tibm/clock/power_values.md

# Power & Passive Values (schematic-ready)

Component values derived from the datasheets in [`/datasheet`](datasheet/) for **this design's** rails.
Everything here is computed for our operating points (VBUS 15 V, 1S Li-ion, the rail set in
[`power.md`](power.md)). ⚠️ = verify/validate on bench or against the noted datasheet section.

---

## 1. LT3652 — 1S buck charger (VIN = VBUS 15 V, float 4.05 V, I_CHG 1.0 A)
Datasheet `charger_lt3652.pdf`. V_FB reference = **3.3 V**. Float set by a divider BAT→V_FB→GND.

| Item | Value | Basis |
|---|---|---|
| **R_FB1** (BAT→V_FB, top) | **45.3 k** (1 %) | V_BAT = 3.3·(1+R_FB1/R_FB2); ratio 0.2265 → 4.047 V |
| **R_FB2** (V_FB→GND, bottom) | **200 k** (1 %) | divider drain ≈ 16.5 µA (always-on, even on battery) |
| **C_FF** feedforward | **22 pF** C0G, BAT→V_FB | datasheet: 20–50 pF to reject V_FB stray-C noise |
| **Full-charge FET** (Decision #2) | **976 k** (1 %) in ∥ with R_FB2, switched by a **2N7002** NMOS | ON → 4.20 V "full"; OFF → 4.05 V health cap. Gate = `FULLCHG_EN` (expander) |
| **R_SENSE** (SENSE–BAT) | **0.1 Ω**, ≥0.25 W (2010/2512) | R_SENSE = 0.1 V / I_CHG(max) → I_CHG = 1.0 A (~0.3 C, cool, safe for any cell) |
| **C_TIMER** (TIMER→GND) | **0.1 µF** | ≈3 h EOC; precondition timeout = t_EOC/8 ⚠️ verify vs. TIMER eq. |
| **Inductor** (SW) | **10 µH**, I_sat ≥ 2 A, low DCR | L=(10·R_SENSE/ΔI)·V_FLT·[1−V_FLT/V_IN], ΔI=0.3 → 9.9 µH |
| **Rectifier** (SW→GND) | **Schottky ≥1 A / ≥30 V** (B340A, 40 V/3 A) | I_D > I_CHG·(V_IN−V_PRE)/V_IN = 0.81 A; V_R > V_IN |
| **C_BOOST** (BOOST→SW) | **1 µF** X7R | + refresh Schottky BAT→BOOST (BAT46); no zener (float < 8.4 V) |
| **C_VIN** | **2×10 µF / 25 V** X7R low-ESR | RMS ripple = I_CHG/2 = 0.5 A worst case; TVS SMAJ22CA already on VBUS |
| **C_BAT** | **10 µF/10 V X7R + 100 µF/10 V polymer** | 100 µF bulk **required** because we run system load with no cell |
| **VIN_REG UVLO** | R_IN1 = **316 k**, R_IN2 = **100 k** | V_IN(min) = 2.7·(R_IN1/R_IN2 + 1) ≈ 11.2 V → charger backs off if the 15 V contract sags. *(Alt: tie VIN_REG→VIN to disable.)* |
| **NTC** | NCP18XH103 (10 k, B25/50 = 3380) NTC→GND **+ 909 Ω (0.91 k, 1 %) in series** | LT3652 NTC pin **sources 50 µA**; trips at **1.36 V (0 °C, cold)** / **0.29 V (40 °C, hot)**. Bare 10 k → 0/40 °C; **datasheet: adding 0.91 k series raises the hot cutoff to 45 °C** → **0/45 °C window** ✓ (cold end ≈ 0 °C, series R negligible there) |

> ⚠️ **Constraint:** the LT3652 needs **V_IN ≥ V_BAT + 3.3 ≈ 7.35 V** to charge. So charging (and
> **no-cell operation**) works **only on the 15 V PD contract**. On the 5 V fallback the charger
> idles — the system then requires a cell. Document on silkscreen/firmware.

---

## 2. CH224K — USB-PD sink (request 15 V)
Datasheet `pd_sink_ch224k.pdf` §5.2.1 / §6.1. Single-resistor mode.

| Item | Value | Basis |
|---|---|---|
| **CFG1** (→GND) | **56 kΩ** | table: 6.8 k=9 V · 24 k=12 V · **56 k=15 V** · NC=20 V |
| **CFG2, CFG3** | **NC** (floating) | single-resistor mode |
| **VDD** | **1 kΩ** from VBUS + **1 µF** VDD→GND | datasheet ref schematic |
| **VBUS sense pin** | **10 kΩ** series to VBUS rail | — |
| **PG** (open-drain) | **10 kΩ** pull-up to 3V3 → `PD_PG` (expander) | active-low power-good |
| **CC1 / CC2** | to Type-C CC1 / CC2 | CH224K provides the PD/CC |
| **DP / DM** | **short together at CH224K**; route Type-C D± to **ESP32 IO19/20** | §5.5 PD-only mode → native USB free for the MCU |

---

## 3. TPS61023 — 5 V boost (from BAT, always-on)
Datasheet `boost_5v_tps61023.pdf`. V_REF (FB) ≈ **0.6 V**. Load ≈ 0.5–1.0 A worst case (feeds 3V3 buck + stepper VM + 7× SK6812 ≤0.6 A all-white + EM14 encoder ~30 mA) — well inside the 3.7 A valley limit.

| Item | Value |
|---|---|
| **R1** (VOUT→FB) | **732 k** (1 %) — datasheet 5 V value |
| **R2** (FB→GND) | **100 k** (1 %) → V_OUT = 4.99 V |
| **C_FF** (∥R1) | **220 pF** *optional* (only if loop rings; f_z ≈ 1 kHz) |
| **L1** | **1 µH**, I_sat ≥ 2 A, low DCR (Coilcraft XEL4030-102ME / Würth 74438357010) |
| **C_IN** | **10 µF / 10 V** X7R |
| **C_OUT** | **2 × 22 µF / 10 V** X7R |
| **EN** | tie to **BAT** (rail is always-on) |

---

## 4. TLV62569 — 3.3 V buck (from 5 V)
Datasheet `buck_3v3_tlv62569.pdf`. V_FB = **0.6 V**. V_OUT = 0.6·(1+R1/R2).

| Item | Value |
|---|---|
| **R1** (VOUT→FB) | **453 k** (1 %) |
| **R2** (FB→GND) | **100 k** (1 %) → V_OUT = 3.32 V |
| **C_FF** C3 (∥R1) | **6.8 pF** (datasheet rec for R2 = 100 k) |
| **L** | **2.2 µH**, I_sat ≥ 2.6 A (Table-4 "++" combo) |
| **C_IN** | **10 µF / 10 V** X7R |
| **C_OUT** | **22 µF / 10 V** X7R |

---

## 5. TPS55340 — 12 V boost (from BAT, **plugged-only**, audio PVDD + wake LEDs)
Datasheet `boost_12v_audio_tps55340.pdf`. V_REF = **1.229 V**. Datasheet worked a 12 V/1 A example — reuse it.

| Item | Value | Basis |
|---|---|---|
| **R1** (VOUT→FB) | **86.6 k** (1 %) | V_OUT = 1.229·(1+R1/R2) = 11.87 V |
| **R2** (FB→GND) | **10 k** (1 %) | — |
| **R4** (FREQ/RT) | **95.3 k** → **500 kHz** | datasheet Eq 1 |
| **C_SS** (soft-start) | **0.047 µF** | datasheet |
| **Comp: R3 / C4 / C5** | **2.55 k / 0.1 µF / 100 pF** ⚠️ | 6 kHz BW example; validate on bench |
| **Inductor** | **4.7 µH**, I_sat ≥ **6 A**, low DCR ⚠️ | boost from 1S: I_IN ≈ 4–4.7 A |
| **Diode** (SW→OUT) | **Schottky ≥3 A / ≥30 V** (B340A/B340B, 40 V/3 A) | peak ~5 A |
| **C_OUT** | **3 × 22 µF / 25 V** X7R (1210) | 60 mV ripple, 30 µF eff. after derating |
| **C_IN** | **10 µF/10 V X7R + 0.1 µF + 100 µF/10 V bulk** | high input current |
| **EN** | `BOOST12_EN` (expander) + **100 k pulldown** (off at boot) | true shutdown; **plugged-only** — firmware asserts only when `PD_PG` is live (off on battery) |

> ⚠️ **Constraint:** boosting a single cell (3.0–4.2 V) to 12 V at ~1 A draws **~4–4.7 A input**,
> near the TPS55340's 5.25 A FET limit at low battery → max ~0.9–1 A (≈10–12 W). Even plugged, the
> input is the BAT node (~4.05 V), so the **~12 W ceiling holds** and is now **shared by wake LEDs +
> audio** → firmware keeps their sum ≤ ~12 W (the amp's power foldback covers any shortfall). On
> battery the boost is **off** (plugged-only); the amp drops to the 5 V rail (§8 mux). Don't spec >12 W.

---

## 6. Small analog / support networks

| Block | Values |
|---|---|
| **32.768 kHz XTAL** (ABS07, C_L 12.5 pF) | 2 × **18 pF** C0G load caps (= 2·(C_L − C_stray), C_stray ≈ 3 pF); no series R; ESR ≤ 70 kΩ |
| **Vbat ADC divider** (+ disconnect FET, Decision #3) | R_top **100 k**, R_bot **100 k** (÷2: 4.2 V→2.1 V, ADC1 11 dB atten) + **100 nF** at node. **2N7002** in series with R_bot→GND, gate = `VBAT_DIV_EN` (expander) → off in deep-sleep (saves ~21 µA). **D13 BAT42W (SOD-123)** clamp, cathode on the node → bounds a reversed-cell excursion to ~−0.2 V (added 2026-07-21) |
| **CELL_TEST** (full-cell vs no-cell, added 2026-07-21) | Expander GPB7 → **Q8 2N7002** (gate PD **R26 100 k**) pulls **Q9 AO3401A**'s gate low (G-S pull-up **R27 100 k**); Q9 source = holder+, drain = Q2's gate → asserting lifts Q2's gate to holder+ → **Q2 off**. ADC step at switch-off ≥ ~0.3 V ⇒ empty holder (body-diode back-feed); ≤ ~50 mV ⇒ real cell. Plugged-only, brief; POR-safe (both FETs default off) |
| **USB D± ESD** (added 2026-07-21) | **USBLC6-2SC6** flow-through at J1: D− → pin 1 / out pin 6 → IO19, D+ → pin 3 / out pin 4 → IO20, GND pin 2. **VBUS pin 5 = NC on purpose** — our VBUS is the 15 V contract vs the pin's 5.25 V rating; the internal zener still clamps, and a cable VBUS-to-D± fault burns the (sacrificial) array instead of pumping a rail |
| **QRE1113GR homing** | IR-LED ballast **150 Ω** (V_F 1.2 V → I_F ≈ 14 mA @ 3V3); phototransistor collector→3V3 via **10 k**, output→ADC (IO2) + **100 nF**. Tune 10 k for distance/reflectivity |
| **Reverse P-FET** (AO3401A) | source=holder+, drain=system BAT+; gate→GND **100 k**; optional 8–10 V Zener gate-source clamp |
| **Protector** (HY2111 + AOSD32334C) | **R1** (batt+→VDD, supply stabilize/ESD) **100 Ω** + **C1** (VDD–VSS) **0.1 µF** (datasheet §10: R1 100–200 Ω — too large degrades detect accuracy and risks VDD abs-max on a reversed charger; C1 ≥ 0.01 µF); **R2** (CS→P−, charger/current sense) **2 kΩ** (§10: 1–2 kΩ — larger can prevent cutting charge current with a high-voltage charger); AOSD32334C dual-N in cell− path, gates from **OD** (discharge FET) / **OC** (charge FET). **No external delay caps** — HY2111 delays are internal. Thresholds fixed by suffix **-GB = OV 4.28 V (rel 4.08) / OD 2.90 V / OC 150 mV**. SOT-23-6 pinout: OD1·CS2·OC3·NC4·VDD5·VSS6 *(same arrangement as the replaced AP9101C — nets unchanged)* |
| **Knob (EM14A0D-C24-L064S, 5 V)** | A/B outputs are 5 V logic → **divider 100 k series + 200 k → GND** per channel (node ≈ 3.2 V → IO47/48 PCNT; ~67 k source Z is fine at ≤ a few hundred Hz quadrature); **ENC_SW** dry contact → **10 k PU to 3V3 + 100 nF** at IO17 (+ ~5 ms FW debounce) |
| **I²C pull-ups** | main board **4.7 kΩ ×2** (SDA/SCL) @ 3V3. Sensor breakouts add 10 k each in ∥ — lift their jumpers if the bus gets too strong |
| **ESP32 EN** | **10 kΩ** PU + **1 µF** to GND (+ optional reset button) |
| **ESP32 straps** | IO0: **10 kΩ** PU (+ boot button); IO45/IO46 (the wake PWM lines) sit low at boot via their AO3400A gate nets (R105/R107 = 100 Ω + 10 k ≈ **10.1 kΩ to GND** at the pin) + the S3 internal strap PD — **no dedicated pulldown** (R52 dropped 2026-07-25 as redundant); IO3 internal |

---

## 7. Decoupling plan (per IC)

| IC / rail | Decoupling |
|---|---|
| ESP32-S3 3V3 | **10 µF + 22 µF + 0.1 µF** (module bulk) + 0.1 µF per 3V3 pad |
| TAS5760M | PVDD **0.1 µF + 1 µF + 100 µF/25 V** bulk (C172; **was 220 µF** — no ≥16 V 220 µF exists in the board's Ø6.3 mm SMD can, Panasonic/Nichicon start at Ø8, so the value dropped 2026-07-27 to a **Rubycon 25TZV100M6.3X8** low-ESR part, 300 mA @100 kHz. ⚠ bench: watch PVDD sag on alarm transients; the fix if it sags is a Ø8 land + 220 µF/16 V, not a bigger ceramic); DVDD/AVDD **0.1 µF + 10 µF**; bootstrap + output filter per datasheet |
| TB6612FNG ×2 | VM **0.1 µF + 10 µF**; VCC **0.1 µF** |
| MCP23017 | **0.1 µF** |
| SK6812 chain (7×) | **100 nF at every pixel VDD** + **100 µF bulk** at the chain head; SN74AHCT1G125 **100 nF** |
| Each regulator | in/out caps per §1–5 + 0.1 µF at each VIN pin |

---

## 8. LED subsystem (two rails — see [`led.md`](led.md) + [`power.md`](power.md) §LED)
**2 wake PWM channels + 1 NeoPixel data line** (v0.19 — the 5 V discrete panel string + its 3rd
AO3400A were dropped with the display).

| Channel | Emitter (per `led.md`) | Rail | Pin |
|---|---|---|---|
| **Wake warm** | Inspired LED `12V-COB-3000K-12M` (warm 3000K COB) | **12 V** (plugged-only) | **IO45** (LEDC) |
| **Wake cool** | Inspired LED `12V-COB-4000K-12M` (neutral 4000K COB) | **12 V** (plugged-only) | **IO46** (LEDC) |
| **Status + dial NeoPixels** | **7× SK6812 RGBW 5050** (Adafruit 2758): 5 status + 2 dial | **5 V** (always) | **IO7** (RMT data) |

- **Wake (12 V COB):** `MCU PWM → 100 Ω → AO3400A gate`; `10 kΩ` gate→GND; strip− to FET drain, strip+
  to **12 V**. Self-ballasted (integrated series R) → no external ballast. Keep combined wattage so
  **LED + audio ≤ ~12 W** (TPS55340 ceiling from 1S). ~1 kHz, gamma-corrected.
- **NeoPixels (5 V):** IO7 → **SN74AHCT1G125** (VCC = 5 V; TTL V_IH 2 V ← 3.3 V GPIO OK; the SK6812
  V_IH = 0.7·VDD = 3.5 V is why the buffer exists) → **330 Ω** series → DIN(1); DOUT(n)→DIN(n+1);
  **100 nF per pixel + 100 µF bulk**. `led_strip` (RMT, 800 kHz); ≤~0.6 A all-white worst case.

**Panel string (Cree CLM3C ×≤12 + 180 Ω each + 3rd AO3400A) dropped 2026-07-19.** MOSFET **AO3400A** ×2.

### Amp PVDD rail-mux (12 V ↔ 5 V) — enables the battery alarm
The 12 V boost is **plugged-only**, so on battery the TAS5760M PVDD falls back to the **5 V rail**
(~3 W, quieter alarm). **LTC4412 ideal-diode on the 5 V leg + Schottky on the 12 V leg**; 12 V wins when
present. Pinout (TSOT-23-6): **1 VIN · 2 GND · 3 CTL · 4 STAT · 5 GATE · 6 SENSE**.

| LTC4412 pin / part | Connect to | Basis |
|---|---|---|
| **VIN** (1) | **5 V** rail | primary (backup) source; +**0.1 µF** to GND |
| **SENSE** (6) | **PVDD** node | senses load vs VIN (20 mV fwd-reg / 20 mV reverse-turn-off); +**0.1 µF** |
| **GATE** (5) | gate of **Q_5V** | drives the 5 V→PVDD ideal-diode P-FET (gate clamp V_G(ON) = 7 V) |
| **Q_5V** P-FET | **AO3401A** (reuse) — source = 5 V, drain = PVDD | low-loss; ~36 mΩ×0.6 A ≈ 22 mV → PVDD ≈ 4.96 V (> 4.5 V min). Body diode reverse-blocks when PVDD > 5 V. Lower-R_DS alt (e.g. DMP3017SFG) if tighter reg wanted |
| **CTL** (3) | **GND** | fully automatic SENSE-based switchover (no MCU/expander line) |
| **STAT** (4) | **470 k → 3V3** (optional) or NC | open-drain "12 V-present" flag; can land on a spare expander IN |
| **12 V leg** | 12 V-boost OUT → **Schottky (SS34 / B340A, 40 V, ≥1.5 A)** → PVDD | 12 V has margin for the ~0.4 V drop (PVDD ≈ 11.6 V plugged); blocks 5 V↔12 V back-feed |
| **PVDD bulk** | keep the §7 `0.1 + 1 + 100 µF/25 V` at the amp | mux output = PVDD node |

When 12 V is up, PVDD rises to ~11.6 V > VIN(5 V) → LTC4412 turns Q_5V off (its body diode is also
reverse-biased) → amp on 12 V. On battery the Schottky blocks and Q_5V ideal-diodes 5 V→PVDD.
> A plain 2-diode OR is **rejected**: 5 V − V_Schottky ≈ 4.6 V ≈ the TAS5760M PVDD 4.5 V min (no margin) —
> hence the low-loss FET on the **5 V** leg; the Schottky is only tolerable on the **12 V** leg.

## 10. TAS5760M — control-mode straps, PBTL, gain, output filter (schematic-ready)
Datasheet `amp_tas5760m.pdf` (32-pin DAP). **Software (I²C) control**, **PBTL mono** into the 4 Ω DMA58-4.

| Item | Setting | Basis |
|---|---|---|
| **Control mode** | **Software/I²C** → tie **SPK_GAIN0 (11) + SPK_GAIN1 (12) HIGH to DVDD** (one 10 k pull-up serves both). This reallocates **PBTL/SCL (9) = SCL** and **FREQ/SDA (8) = SDA** as the I²C port | §8.4.2 |
| **I²C address** | **0x6C** → **SPK_SLEEP/ADR (13) → GND** (weak PU, latched at power-up; HIGH = 0x6D). Prep a **0 Ω to GND** | §8.4.2.5.1 |
| **PBTL enable** | firmware sets **reg 0x06 bit 7 = 1** (default 0 = BTL); channel-select = 0x06 bit 1. ⚠ **Corrected 2026-09-13** — the external tie is **OUTA+(29)∥OUTA−(26)** as one leg and **OUTB+(20)∥OUTB−(23)** as the other, speaker between them (datasheet Fig. 64/65). This row previously said OUTA+∥OUTB+ / OUTA−∥OUTB−, which is **wrong**: it shorts a high side to a low side and puts a PVDD→PGND path through 2×120 mΩ every switching cycle. **The board was already right** — `kicad/REVIEW.md` fixed #2 caught it in the schematic (`1f3736a`, refined `1cf1629`) and the PCB followed in the 2026-08-04 sync + routing; only this line was left stale | §8.4.2.3 |
| **Analog gain** | firmware **A_GAIN[3:2] in reg 0x06**; start **19.2 dBV** (matches 12 V PVDD). ⚠ **Digital boost = +0 dB, NOT the default** — corrected 2026-09-13: reg 0x02[5:4] powers up at **01 = +6 dB**, and [`FIRMWARE.md`](FIRMWARE.md) §6.2's whole ceiling table is computed from *0 dBFS = 9.12 V rms*, which is 19.2 dBV **with no boost**. Leaving the default makes every watt in that table 6 dB optimistic, and the 8 W inductor cap depends on it. The firmware writes `0x02 = 0x04`. (SW mode: gain is a register, not a pin) | §8.4.2.4 |
| **Output LC (4 Ω)** | **10 µH + 0.68 µF per leg** (datasheet 4 Ω filter; 8 Ω = 22 µH, 6 Ω = 15 µH), f_c ≈ 30–40 kHz. **L5/L6 = XAL4040-103MEC, Isat 3.0 A** and they carry the full speaker current; the OCE trips at 7 A/BTL (**~14 A in PBTL**), so the amp cannot protect them → the **firmware limiter is capped at 8 W into 4 Ω** (peak 2.0 A + 0.38 A ripple ≈ 79 % of Isat), [`FIRMWARE.md`](FIRMWARE.md) §6.2 | §6.13 |
| **SPK_SD (7)** | from **MCP23017 GPA0** (idle-low = shutdown at boot) | §8.4.2.1 |
| **SPK_FAULT (6)** | open-drain → **10 k PU to 3V3**; optional to a spare expander IN (GPB6) for a HW fault line, else poll fault regs over I²C | §8.3.3.1 |
| **SFT_CLIP (2)** | **tie to GVDD_REG** (soft-clipper off → clip at rail; firmware HPF + limiter + digital clipper protect the driver). Divider+cap only if a fixed soft-clip point is wanted | §8.4.1.3 |
| **Reg pins** | ANA_REG(3)/GVDD_REG(32)/VCOM(4)/ANA_REF(5): **bypass caps only — do not load** | §8.3.1 |
| **AVDD (1)** | ⚠ **→ PVDD, NOT +3V3.** Added 2026-09-14 after build #1 made no sound. §6.3 Recommended Operating Conditions gives **AVDD 4.5–26.4 V** — the same range as PVDD; only **DVDD** is 2.8–3.63 V. §10's prose ("two power supplies") reads as if there were no third supply pin, and that is the trap: three supply PINS, two RAILS. Figure 64 routes pin 1 to the PVDD node. **The board ties it to +3V3 — 1.2 V under minimum** — which leaves the digital domain alive (I²C fine) and the analog domain dead (reg 0x08 stuck at CLKE). `kicad/REVIEW.md` **V13** carries the fix and the bench bodge | §6.3 / Fig. 64 |
| **MCLK (14)** | TAS5760M **requires MCLK (128–512 × f_S)** — not MCLK-less. **`IO43` = `I2S_MCLK`** (HW I²S0 via the S3 GPIO matrix; reassigned from the aux UART log → logging = USB-CDC only). Target **256 f_S ≈ 12.288 MHz @ 48 kHz** | §8.3.2.1 / Table 6 |

---

## 9. Speaker output filter (Decision #4 → **LC, recommended**)

| Option | Per BTL output | ~Cost | Trade |
|---|---|---|---|
| **Full LC** ✅ | **L 10–22 µH + C 0.68–1 µF** (f_c ≈ 30–40 kHz), ×2 legs | **+$1.0–1.5** + ~1 cm² | Clean, EMC-robust, tolerates longer leads; TI recommends it for PBTL |
| Ferrite-bead "filterless" | ferrite bead + small cap ×2 | +$0.10 | Cheapest/smallest, but the wood enclosure doesn't shield and 400 kHz on the speaker leads risks radiated-emissions failure — only OK with very short leads |

**Recommendation: full LC.** $1 of insurance for EMC + clean sound on a quality bedroom alarm.

---

## Still open (needs a decision, datasheet, or bench)
- **LTC4412 PVDD mux — RESOLVED** (§8): ideal-diode FET (AO3401A) on 5 V + Schottky on 12 V, CTL=GND. Bench: confirm wake-COB wattage keeps **LED + audio ≤ ~12 W**.
- **L5/L6 saturation headroom — RESOLVED in firmware 2026-07-27** (§10): DSP limiter capped at **8 W into 4 Ω** = −4.1 dBFS at the 19.2 dBV analog gain. **Recompute the dBFS ceiling if A_GAIN or the 12 V setpoint moves.** Bench: current probe on L5 at max volume.
- **TAS5760M — RESOLVED** (§10): SW/I²C (GAIN pins HIGH), addr 0x6C, PBTL reg 0x06[7], gain 19.2 dBV, LC 10 µH + 0.68 µF (4 Ω). **MCLK on IO43** (reassigned from the aux UART log; HW I²S0 via the S3 GPIO matrix, ~12.288 MHz) — logging = USB-CDC only. **Driven in firmware since 2026-09-13** (`FIRMWARE.md` §12.0.15): the register set is `0x01=0xFD 0x02=0x04 0x03=0x80 0x06=0xD1`, written in the datasheet's §9.2.1.2.1 order, and `audio status` prints it back. ⚠ Still bench-unverified — nothing has been through a speaker.
- **TB6612 — RESOLVED** (`esp32.md` pinout table): PWMA/PWMB tied HIGH to Vcc (PWM-on-IN); coil AO/BO → X40 contacts mapped.
- **LT3652 NTC — RESOLVED** (§1): 10 k NTC **+ 0.91 k series** → 0/45 °C.
- **TPS55340 comp network** — values in §5; validate on bench.
