tibm/clock/kicad/REVIEW.md

# Design review — `clock.kicad_sch` / `clock.kicad_pcb`

**Date:** 2026-08-02 · **Reviewed at commit:** `7ec2534` ·
`clock.kicad_sch` md5 `923072dddf48824cfdb7de3341dcab70` ·
`clock.kicad_pcb` md5 `8620b590d079f6193cd99e7b7b5c9549`

**Scope:** functional/electrical correctness of the main-board schematic and PCB,
cross-checked against the datasheets in `datasheet/`. Mechanical/3D fit, the custom
footprints vs. vendor drawings, silkscreen legibility, and the sensor board's own
internals are **not** covered.

> **Pruned 2026-08-08.** The write-ups of findings that are **fully closed**
> have been deleted from this file — the fix is in the design files, and the
> reasoning that outlived it is in `PCB_NOTES.md`. Gone: **#1, #2, #3** (Q4,
> PBTL pairing, `C104`), **#5** (thermal vias), **#9** (`C238`), **#10–#13,
> #15, #17, #19–#21, #23**, and the Phase-2 PCB work order. The status tables
> below still list every one of them with its commit. What is kept in full is
> the work that is **still live** — #4, #6, #7, #8, #14, #16, #18, #22, #24,
> #25 — plus the "checked and found correct" record.

## Verification baseline

```
kicad-cli sch erc --severity-all clock.kicad_sch   → 0 violations
kicad-cli pcb drc --severity-all clock.kicad_pcb   → 0 violations, 0 unconnected
```

Everything below is what those tools structurally cannot see. Findings were derived
from the exported netlist, a parse of the `.kicad_pcb` (pads / tracks / vias / zone
fills), and the vendor datasheets.

## ⚠ Workflow note before touching anything

`gen/pcb_build.py` calls `pcbnew.CreateEmptyBoard()` and overwrites
`clock.kicad_pcb`. The board now contains **1884 track segments, 555 vias and four
filled GND zones** that the generator never produced (added by the autorouter +
manual passes, commits `91c5087` … `129a757`). **Re-running `pcb_build.py` destroys
all routing.**

- **PCB sync** — `gen/sync_pcb.py` is the headless stand-in for *Update PCB from
  Schematic* (KiCad 10 exposes no netlist updater to Python and `kicad-cli pcb` has
  no such subcommand). It applies values, footprint swaps, new parts and pad nets,
  and cuts **only** the copper that would otherwise short two nets. It never adds
  copper. Idempotent — a second run reports 0 changes.
- **Schematic** — still generator-driven: edit `gen/b_*.py`, then
  **`build.py` followed by `stamp_bom.py`**. `build.py` alone drops the 684
  MPN/Manufacturer/Package/Notes properties that `stamp_bom.py` writes; the BOM
  fields come back only when it is re-run (its own docstring says so).
- **PCB** — now hand-owned: edit in pcbnew, propagate schematic changes with
  *Tools → Update PCB from Schematic* (F8). `pcb_build.py` is a one-shot placement
  tool that has been superseded; `PCB_NOTES.md` ("no traces are routed") is stale.

---

## 🔵 v0.4 — carried out of rev0.3 bring-up

Everything here was found by **building and running board #1**, not by review. Source: the
bench notes in [`../PCB_v0.3_learnings.md`](../PCB_v0.3_learnings.md) plus what the firmware
bring-up measured (`FIRMWARE.md` §12.0.3–§12.0.6). None of it is urgent — rev0.3 works — but
none of it should be rediscovered.

> ✅ **V9, V13, V14 and V15 are all fitted on build #1** as of 2026-09-27 (they were reworks
> R1–R4; the bench guide has been retired into `FIRMWARE.md` §12.0.17, which carries the
> outcome, the coordinate card and the cell-insertion SOP). The board charges, plays and runs
> off the cell. This table is the *why*, and it is still the authoritative v0.4 list.
>
> ⚠ **V9 + V14 + V15 + V16 are one fix wearing four hats** — the protector's sense loop. Fitting
> any one alone leaves the board tripping on insertion and refusing to charge; build #1 proved
> that with V9 on 2026-09-22 and again with V14 (R3) on 2026-09-27, both of which changed
> nothing observable by themselves. See the correction note under V16.
>
> ## 🔒 How v0.4 is prevented from repeating this
>
> **Every one of V13, V14 and V15 passed ERC and DRC without a murmur**, and V14 also passed
> this file's own finding #4 — which asks whether *some* net got widened, not whether the right
> ones did. Prose findings did not prevent them and will not prevent the next one.
>
> The gate is **`gen/review_check.py`**, which already existed for the 2026-08 review findings
> and now carries the V-series. Run it before a respin is fabbed; it exits non-zero on a
> regression, and reports `TODO` for what is known-open:
>
> ```
> cd gen && python3 review_check.py        # 22 checks, 0 regressions as of 2026-09-27
> ```
>
> | check | asserts | the bug class it catches |
> |---|---|---|
> | `V13` | `U9.1` is on the same net as `U9.28`, and not on `DVDD`'s | **a legal net on the wrong pin.** No rule engine flags `+3V3`; only the pin's datasheet range does |
> | `V14` | each cell-current net computes ≤ 10 mΩ from the routed copper | **a correct net at the wrong width.** Resistance, not "is it wider than default" |
> | `V14b` | both are in `POWER`'s `netclass_patterns` *by name* | the string match that failed. Both nets are auto-named on rev0.3 |
> | `V15` | `R21`'s cold end is on `U4.1`, not `GND` | **a sense tap on the wrong node** — topology, which no width or clearance check sees |
> | `V15b` | `R21` ≤ 2 kΩ, against the measured 250 kΩ internal pull-up | a value that silently eats the threshold budget |
> | `V16` / `V16b` | 3.7 A and 2.3 A × loop < `V_DIP` floor; 1 A × loop < 60 mV | **the margin arithmetic itself** — the check none of the others replace |
> | `V17` | a release switch exists, or `U3` is a `-KB` | a requirement the schematic cannot express |
>
> Its constants (`I_BOOST_STARTUP_A`, `R_FET_PAIR_MOHM`, `V_DIP_MIN_MV`, …) are declared at the
> top of the file with their sources, so the arithmetic can be re-derived rather than trusted —
> which is the actual lesson of §12.0.13 and of V9's wrong divisor.
>
> ⚠ **What the gate still cannot check**: that the *right* nets are listed in `CELL_PATH_NETS`
> in the first place. That list is hand-written, and a future net carrying cell current would
> have to be added to it. The generator-side answer is to name the conduction path explicitly
> in `b_charger.py` (V14) so the list is derivable rather than remembered.

| # | Change | Cost | Why |
|---|---|---|---|
| V1 | **`M1` lower snap peg: (0, 9.62) → (0, 11.62)** — 2 mm further from the shaft | one footprint edit | **Required hand rework on build #1.** The two top pegs at (±8.49, −8.49) and the Ø4.6 shaft hole at (0, −6) are all correct; only the lone bottom peg is off. Edit `clock.pretty/Juken_X40-879_DualShaft.kicad_mod`, then re-verify against the factory STEP — the peg was derived from it, so a 2 mm error suggests the reference, not the transcription |
| V2 | **`R99` 10k → 22k** (QRE1113 collector pull-up) | one resistor | Doubles the homing signal *and* moves the clear end out of the ADC's clipped region. Measured on rev0.3 (R99 = 10k, 3.3 V rail): nothing 3159 mV\* / minute-hand distance 3010 / hour-hand distance 2600 / covered 2200 — i.e. 14, 29, 70, 110 µA of photocurrent. The weakest signal that matters is the **149 mV** minute-hand step. At 22k it becomes **~330 mV** with the clear end at ~2990 mV, in range. 33k gives ~490 mV but saturates on full cover. *\*3159 is clipped: 12 dB attenuation tops out near 3100* |
| V3 | **`J2` gains a +5 V pin** — bench power and flashing from one header | 1×04 → 1×05/06 header, one net | "Flashing is painful." A Mac cannot power this board at all (§12.0.3: VBUS reaches only the LT3652, which idles below 11.2 V), so bring-up means injecting 5 V at **`J12`** — the status-LED connector — while USB carries data. A labelled 5 V pin on the programming header replaces that hack. **Pin order is the actual design question:** 5 V next to +3V3 or to IO0 on an unkeyed 0.1″ header means one slipped position puts 5 V on a 3.3 V pin or an ESP32 GPIO. `GND · +5V · GND · +3V3 · EN · IO0` (1×06) is slip-tolerant; `+3V3 · GND · EN · IO0 · +5V` keeps the existing four positions but puts 5 V beside IO0, which is the worst neighbour |
| V4 | **Sensor harness: make reversal non-destructive** | 1×08 on both boards + re-route J7 | A reversed cable **actually arrived** for build #1 (2026-09-08) and was caught by a continuity check, not by the design. §4 below rejected a 1×07 twice on cost; the new evidence is that the hazard is real, not theoretical. The insight the earlier rounds missed: **the damage comes from power landing on a signal pin, not from signals being swapped.** A *palindromic* 1×08 — `GND · SDA · SENSOR_INT · +3V3 · +3V3 · ALS_INT · SCL · GND` — survives reversal outright: GND meets GND, +3V3 meets +3V3, and only SDA↔SCL and the two INTs swap. The failure mode becomes "scan finds nothing", which is safe, obvious and diagnosable, instead of a dead $13.57 BNO085 |
| V5 | **Gate the QRE1113 LED** from a spare expander pin (GPA4-6 are free) | one FET + one net | Buys two things with one change. Power: it is a permanent **14 mA** draw, which #14 already wants gated for backup runtime. Accuracy: with the LED switchable, firmware can read LED-on minus LED-off and **cancel ambient IR entirely** — worth having, because bench readings of the same "nothing in front" condition moved ~500 mV between two sessions under different room lighting. In the sealed cube ambient is close to zero, so this is an improvement rather than a fix |

| V6 | **Bring `USB_D±` out to `J2`** — the programming header carries data as well as power | 2 nets to the existing header (pairs with **V3**) | **The board cannot be powered and talked to at the same time.** `J1` is the only power inlet *and* the only console: the console is USB-CDC only — `TXD0`/`IO43` became `I2S_MCLK` and `RXD0`/`IO44` is the expander IRQ, so there is no UART to fall back on — and USB-Serial-JTAG lives on `IO19`/`IO20` → `J1`'s `D±`. A Mac will not source the 15 V the LT3652 needs and a PD brick carries no data, so **power bring-up has no live console at all** (`FIRMWARE.md` §12.0.11). Today's workaround needs no rework at all: an **inline USB-C male-to-female pass-through** between brick and `J1`, tapping `D±`+GND to the host, with the host's `VBUS` unconnected and `D±` cut on the brick side (`FIRMWARE.md` §12.0.11 has the rig and its three conditions). With `D±` on `J2`, `J1` takes the PD brick and `J2` takes the host — which also retires the `J12` 5 V injection hack that V3 is about. ⚠ `D±` is a 90 Ω differential pair: keep the stub short, keep the two lengths matched, and do not route it past the antenna keepout |
| V7 | **Key or label `J10` against end-for-end reversal** | silkscreen at minimum | The knob harness **was** soldered reversed on build #1 (2026-09-10, `FIRMWARE.md` §12.0.10) and it took a firmware diagnostic to find. The ZH connector is **palindromic in its power pins** — reversed, `+5V` and `GND` land exactly where they belong — so the one measurement anybody takes before powering up (5 V across the encoder's `+`/`–`) reads healthy and proves nothing. The damage path is the same one V4 identifies for `J7`: `ENC_SW` has no divider, because a dry contact needs none, so a reversal puts the EM14's **5 V channel `A`** straight onto `IO17` of a part that is not 5 V tolerant. Cheapest fix is a pin-1 arrow and a `– A 1 2 + B` legend beside `J10`; the same palindromic-pinout trick V4 uses would be better still |

| V8 | **[MUST — and V16 gives it a second, independent reason] Gate `U5`'s `EN` on a ~3.0 V supervisor instead of a hard tie to VBAT** ⚠ *V16 (below) makes this one of only two ways to get the 3.7 A boost startup under the protector's `V_DIP` floor; the other is a `-HB`/`-KB`. Copper alone cannot do it.* | one supervisor (or a comparator off the existing `VBAT_SENSE` divider) + one net | **The board cannot cold-start into a 0 V BAT node.** Below `V_FB(PRE)` = 2.3 V (BAT < 2.84 V) the LT3652 clamps to `V_SENSE(PRE)` = 15 mV across `R18` = **150 mA**, but `U5`'s `EN` is tied straight to VBAT, so the 5 V boost, the 3.3 V buck and a booting S3 load the node immediately. 150 mA at 1.3 V is 195 mW for the whole board — below idle — and it sits there until the 33 min bad-battery timer latches it off. Measured on build #1 2026-09-11: BAT 1.3 V / +5 V 2.9 V / +3V3 3.0 V, every feedback divider correct (`FIRMWARE.md` §12.0.12, `power.md`). **Not a bench-only problem:** a deeply-discharged cell on USB never recovers, because the 150 mA goes into the cell while the load draws from it. Raising `I_CHG` cannot fix it (it would need ~2.7 A, over the LT3652's 2 A ceiling and ~0.9 C on a 3 Ah cell) — the load has to be gated, not the charger. Until then, bring-up needs a charged cell in the holder. **This is the single change that makes the board run with no cell at all**, and it also removes the boost's startup surge from the cell-insertion event, which is half of **V9**'s problem. Spec: supply and sense from VBAT (must be defined from 0 V to 4.2 V, tolerate 5.5 V), output HIGH above 3.0 V with hysteresis, LOW below, SOT-23-3 or smaller, drives `U5` pin 2 directly. ⚠ Part not yet chosen — verify active on DigiKey and file the datasheet |

| V9 | **[MUST] Replace `U4` with the AO4838** (30 V dual N, ≤13 mΩ @ VGS 4.5 V, [DK 3152401](https://www.digikey.com/en/products/detail/alpha-omega-semiconductor-inc/AO4838/3152401), ~$1.15) — **pin-identical SOIC-8**, so footprint and netlist are unchanged (same SO-8 dual arrangement: pin 2 gates pin 1's FET, pin 4 gates pin 3's; all four drain pins are tied on this board, so D1/D2 labelling is irrelevant) | one SO-8 part | **One resistance sits at the centre of two independent lockups, and the fix is to make it small.** The HY2111 senses discharge *and* charge current as the drop across the pair. Discharge: `V_DIP` 150 mV (`-GB`) / 52 mΩ = **1.89 A worst case**, under the TPS61023's **3.7 A** valley limit, so the boost trips the protector on every cell insertion — and §11.4 releases only above **450 kΩ** across PB+/PB− (this board is a permanent ~40 Ω) or on a charger, which **V8**'s lockout blocks. Charge: `V_CIP` = **−100 mV typ, −60 mV worst case**; `I_CHG` 1 A × 52 mΩ = 52 mV, i.e. **8 mV of margin** — and 26 mΩ is specified at **VGS = 4.5 V, the datasheet's lowest characterised gate drive**, while VGS here *is* the cell voltage (≤4.2 V), so the part always runs below it. Measured on build #1 2026-09-13: a 3.4 V cell took **zero** charge; `OC` latched off inside `T_CIP` = 12 ms and §11.5 releases only by removing the charger, so it re-trips every replug. **Design rule both ways:** `I_CHG` × R_DS(pair at the lowest cell voltage you must charge from) < 60 mV, and peak discharge × R_DS(pair) < `V_DIP` − 25 mV. Derated as #6 derates (gate drive is V_cell ⇒ R_DS ≈ 1.27× the 4.5 V spec), the AO4838 pair is **26–33 mΩ**: charge 1 A → **33 mV**, 1.8× under the 60 mV worst-case `V_CIP` ✓; boost startup 3.7 A → **122 mV**. ⚠ **122 mV clears `-HB`'s 175 mV floor by 1.4× but sits 3 mV under `-GB`'s 125 mV — so V9 REQUIRES V10, they are one change.** The same arithmetic reproduces both measured failures on the AOSD32334C (244 mV startup vs a 150 mV trip; 66 mV charge vs a 60 mV threshold), which is why it is trusted. Together they move the discharge trip to **5.3–8.7 A** — see the safety note in `power.md`: that is a deliberate loosening, floored by the boost's 3.7 A surge until **V8** (`FIRMWARE.md` §12.0.13, `power.md`) |
| V10 | **[SHOULD] `U3` = `-HB` if obtainable — see V11 before ordering** | BOM/substitution note | Splits typical from worst case. With **V9** fitted the boost's 3.7 A startup lands at 98 mV typical / 122 mV worst: against `-GB` that is **1.53× typ but 1.02× worst**, against `-HB` 2.05×/1.43×. So a `-GB` works on most parts and a worst-case stack still trips **at cell insertion only, costing a one-time bridge rather than damage** — livable, and `-HB` is what makes insertion deterministic. **Charging is fixed by V9 alone**, `V_CIP` being suffix-independent. ⚠ **`-HB` was out of stock at LCSC 2026-09-13 and the HY2111 is the only LCSC-only, single-sourced part in the whole build** — do not make v0.4 depend on it; see **V11**. Legacy rationale: `V_DIP` 200 mV vs 150 mV lifts the discharge trip from 1.89 A to 2.65 A and buys **V9** its margin on the alarm peak. LCSC **C160793**. **Do not accept a `-GB` substitution** — check the marking on arrival |

| V11 | **[MUST] Make `U3` a multi-sourced socket, not a single part** — document the shared SOT-23-6 arrangement on the silk/BOM and buy whatever is stocked at build time | zero board change; a BOM + doc change | **The protector IC is the only single-sourced, LCSC-only part in the build, and it has now been re-picked three times on availability alone** (S-8261 reel-only 3000 MOQ → AP9101C NRND → HY2111 LCSC-only → `-HB` out of stock 2026-09-13). Stop chasing a part and remove the constraint that made only one work. **V8 + V9 do exactly that:** gating the boost drops the worst-case current through the FET pair from the **3.7 A** startup surge to the **2.3 A** sunrise alarm, and at the AO4838's 26–33 mΩ that is **76 mV** — so any protector with `V_DIP` ≥ ~120 mV qualifies, which is essentially the entire 1-cell market (100 / 150 / 200 mV are the standard values). The family also shares one pinout: **`1 OD/DO · 2 CS/VM · 3 OC/CO · 4 NC · 5 VDD · 6 VSS`** in SOT-23-6 — already noted for HY2111 ↔ AP9101C (`power.md`), and the S-8261 and R5478N follow it. Re-check **ABLIC S-8261A** and **Nisshinbo R5478N** at DigiKey *and* Mouser: both were rejected in 2026-07 on availability, not suitability, and neither is LCSC-only. ⚠ Verify the pinout and `V_DIP` of whichever part is actually bought against its own datasheet before committing the BOM — the family convention is strong but not a standard |
| V12 | **[SHOULD] Rename the motor nets for the SHAFT, not the hand** — `STEP_M_*` → `STEP_TUBE_*` (driver #1, MCPWM0) and `STEP_H_*` → `STEP_PIN_*` (driver #2, MCPWM1), in `kicad/gen/b_motor.py` and `esp32.md` | net labels only; zero copper, zero BOM | **The hands swapped shafts on 2026-09-13 and the wiring did not, so both net names are now backwards.** The minute hand went to the X40's inner pin so it reads in front like a normal clock, the hour hand to the outer tube (`cad/README.md`, `FIRMWARE.md` §6.1e) — but driver #1 is still soldered to the tube, so `STEP_M_*` drives the **hour** hand and `STEP_H_*` the **minute**. A net name that asserts the wrong hand is worse than a neutral one: it is the label somebody will trust while probing a coil with a scope, and it disagrees with `board.hpp`, which has already been renamed `step_tube`/`step_pin`. Naming them for the shaft also makes them immune to the next time that decision changes. ⚠ Cosmetic and deferred on purpose: firmware crosses the two in one place (`motor_esp.cpp`'s `build()`, which logs `hour=tube(MCPWM0) minute=pin(MCPWM1)` at boot), so nothing is broken today and `kicad/gen/` keeps matching the board as built |
| V13 | **[MUST] `U9` pin 1 `AVDD` goes to `PVDD`, not to `+3V3`** — delete the wire tying pin 1 to pin 10's net in `kicad/gen/b_audio.py` and take it to the `PVDD` node instead; move `C162` (10 µF) + `C163` (100 nF) with it | one net, two caps re-parented; zero footprint, zero BOM | **The amp is 1.2 V under a supply minimum, and it is why board #1 makes no sound.** `amp_tas5760m.pdf` §6.3 Recommended Operating Conditions: **`AVDD` 4.5 V min / 26.4 V max** — the same range as `PVDD`, *not* the 2.8–3.63 V of `DVDD`. §10's prose ("the device requires two power supplies") is what misleads, and the pin table resolves it: three supply PINS, two RAILS, and `AVDD`+`PVDD` are the same rail. Figure 64 (mono PBTL, software control — the exact topology this board uses) routes pin 1 up and over the package to the `PVDD` node. Ours reads `+3V3 U9.1 AVDD_1` in the netlist. **Symptom on build #1, 2026-09-14:** `DVDD` 3.3 V, `PVDD` 5.0 V, straps correct, I²C perfect (registers read back exactly what was written), all three clocks present and correct **at the amp's own pins** on a scope (MCLK 12.288 MHz, BCLK 1.536 MHz, LRCK 48 kHz, ratios 256/32 — both in Table 6) — and reg 0x08 stuck at `CLKE` with `SPK_FAULT` low. Digital domain alive, analog domain dead, which is exactly what starving `AVDD` looks like: `ANA_REG`/`VCOM`/`ANA_REF` and the clock-validation circuitry all sit in it. ⚠ **The CLKE link is a strong inference, not yet proven** — the spec violation is certain, that it is the sole cause of this symptom is confirmed only when the bodge makes a sound. **Bench bodge for build #1 — cut, do NOT lift.** Verified against `clock.kicad_pcb` 2026-09-14: all four copper zones are **GND**, so there is no `+3V3` pour, and `U9` pad 1's *only* connection to `+3V3` is a single **0.25 mm B.Cu trace, 0.85 mm long**, running in −X from the pad at **(92.850, 83.432)** to a junction at **(92.000, 83.432)**. Cut it at ≈**(92.4, 83.43)** and the pin is fully isolated *with its pad still attached* — so the wire solders to the pad and no pin is ever lifted next to `SFT_CLIP` on 0.65 mm pitch. Nearest other copper to the cut is pin 2's `GVDD_REG` trace, **0.65 mm** away at y = 82.782 — the one thing to keep the blade off. Then wire pad 1 → **`C170` pad 1** (PVDD, 0.9 × 0.9 mm 0603 pad, **10.66 mm** away, same side, essentially a straight run). ⚠ **`C170` pad 2 is GND** — pads 2 of `C170`/`C171`/`C172` are all GND and would short `AVDD` to ground. Verified PVDD pads: `C170.1` (103.50, 83.934) · `C171.1` (106.00, 83.934) · `C172.1` (104.70, 64.014) · `U9.21` (100.15, 76.282) · `U9.28` (100.15, 80.832). **Verify before power:** pin 1↔`+3V3` open, pin 1↔GND open, pin 1↔pin 2 open; after the wire, pin 1↔`U9.28` ≈ 0 Ω. `C162`/`C163` stay behind on `+3V3` as harmless extra bypass; `C170` sits at the tie point. **The cut is reversible** — a wire from pad 1 back to the via at (91.688, 83.101) restores it. ⚠ After the bodge `AVDD` follows `PVDD` **including to 12 V** when the boost is enabled — intended (26.4 V max, 30 V abs max) and what the datasheet does |

| V14 | **[MUST] Put the cell-return nets in the `POWER` netclass — and name them** — `Net-(BT1-Pin_2)` → **`CELL-`**, `Net-(U4-S2)` → **`PACK-`** in `kicad/gen/b_charger.py`; add both (and `+3V3`, also missing) to `clock.kicad_pro`'s `netclass_patterns`; re-route them like `VBAT`, fat on F.Cu | net names + one netclass line + a re-route; zero BOM, zero footprint | **The cell's entire return current is on the 0.25 mm default track, and 111 mΩ of it is inside the protector's sense loop.** `U3` senses `VSS`(cell −) against `CS`(board GND), so the copper between them is part of every current measurement it makes: `VSS` tap → `U4` pin 3 is 6.8 mm @ 0.25 mm (**13 mΩ**) and `U4` pin 1 → `F1` pad 1 is **34.5 mm @ 0.25 mm, 32.7 mm of it on In2.Cu (69 mΩ)** — against an AO4838 pair of 26–33 mΩ. **This is why V9 changed nothing measurable on build #1** (2026-09-22): the swap took the loop from ~145 mΩ to ~120 mΩ, moving the `-GB` trip from ~1.0 A to ~1.25 A against a **3.7 A** boost startup, and left 1 A of charge current at 113–145 mV versus a −60 mV worst-case `V_CIP`. The same copper drives REVIEW #7 / §12.0.13 finding 2: **0.93 W in a trace rated ≈0.7 A** at 3.7 A, and the droop feeds a constant-power boost, which is what holds the loop over `V_DIP` for longer than `T_DIP`'s 5–15 ms. **Why it was missed:** the #4 widening pass matches net *names*, and both of these are auto-named, so `VBAT` (408 → 268 mΩ) and `+5V` (513 → 322 mΩ) were widened while the net carrying the identical current was not. **Do the naming part** — the netclass line is a string match, and a string match is what failed. ⚠ Better still, add a generator assertion that every net on the cell's conduction path computes under a resistance budget, the way `verify_pins()` asserts pad positions. Fitted on build #1 as rework **R3** (`../FIRMWARE.md` §12.0.17); encoded as checks `V14`/`V14b` in `gen/review_check.py` |
| V15 | **[MUST] `CS` goes to P−, not to GND** — route `R21` pad 2 to the `PACK-` node (`U4` pin 1) instead of the pour; `kicad/gen/b_charger.py` line 284 (`s.gnd(R21, "2", drop=0)`), and fix the comment on 281 that encodes the error | one net; zero BOM, zero footprint | **`F1`, the 77 °C one-shot TCO, sits between `U4` pin 1 and the GND pour — so GND is not P− on this board, and the TCO is inside the protector's current-sense loop.** `battery_protector_hy2111.pdf` §10's external-component table puts `R2` (our `R21`, 2 kΩ) on **P−**, the far source of the FET pair, with nothing but the FETs between the two sense nodes. As drawn, the TCO's resistance *and its two joints* are added to both `V_DIP` and `V_CIP` — and a thermal cutoff's resistance is not a specified parameter in `tco_sdf_df077s.pdf`, so the loop carries an **unbounded** term. A TCO is a thermal device; it has no business in a current measurement. Protection coverage is identical after the change — every electron out of the cell still crosses the FET pair, so `CS` still sees all of it — and the TCO keeps protecting the cell in series, outside the loop. With V14 + V15 the loop is the FET pair alone, **26–33 mΩ**, which is the number V9 already claims: `-GB` trips at 3.8–6.7 A and 1 A of charge lands at 26–33 mV, half the worst-case `V_CIP`. Fitted on build #1 as rework **R4** (`../FIRMWARE.md` §12.0.17) — as a bare wire rather than a resistor, which is *more* accurate: the measured 250 kΩ internal `CS` pull-up means any `R21` puts a standing offset on the sense node, so v0.4 should carry **1 kΩ** (the datasheet minimum), not 2 kΩ. Encoded as checks `V15`/`V15b` |

| V16 | **[MUST] Make the margin arithmetic pass, and it needs more than V14 + V15** — either **V8** (gate `U5`'s `EN`, so the 3.7 A boost startup stops being the worst case) **or** a protector with a higher `V_DIP` floor (**`-HB` 175 mV / `-KB` 195 mV**). Pick one deliberately; do not ship having satisfied neither | one supervisor *or* one BOM line | **V14 + V15 are necessary and still not sufficient, and this is the row that says so.** With both fixed at a 10 mΩ/net copper budget the sense loop is `cell-` 10 + FET pair 33 = **43 mΩ**, and the TPS61023's **3.7 A** startup lands at **159 mV** — over a `-GB`'s **125 mV** floor. Copper cannot fix that: even at 0 mΩ of trace the FET pair alone is 33 mΩ ⇒ 122 mV, 3 mV under the floor, which is not a margin. Two ways out, and they are independent: **remove the surge** (V8 gates the boost ⇒ worst case becomes the 2.3 A sunrise alarm ⇒ 99 mV, comfortable even on a `-GB`) or **raise the floor** (`-HB` ⇒ 159 mV vs 175 mV, 10 % margin; `-KB` ⇒ 22 %). ⚠ This also retires the framing of V10: the `-HB` is not "typical vs worst case polish", it is one of only two ways to satisfy V16. **Charging is a separate inequality and copper alone does fix that one** — `V_CIP` is −60 mV worst case and suffix-independent, so 1 A × 43 mΩ = 43 mV passes once V14 + V15 land (confirmed on build #1 2026-09-27: it charges). Encoded as checks `V16`/`V16b` in `gen/review_check.py` |
| V17 | **[MUST] Give the board a deliberate cell-insertion release** — a momentary **`CS`↔`VSS`** short brought out to a switch (needs `R21` fitted, so it stays a signal-level short), **or** an auto-recovery protector (`-KB`). Also: make `R21` **1 kΩ**, not 2 kΩ | one switch, or one BOM line | **`battery_protector_hy2111.pdf` §11.1: *"Discharging may not be enacted when the battery is first time connected. To regain normal status, CS pin and VSS pin must be shorted or the charger must be connected."*** This is how the whole part family behaves, not a defect — but this board satisfies **neither** release condition on its own, so a user replacing an 18650 gets a dead clock. The charger route is blocked by our own safety choice: with the discharge FET off, charge current must cross FET1's body diode, and the LT3652 floats at **4.05 V**, so `4.05 − V_cell > 0.7 V` (AO4838 `V_SD` typ, 1.0 V max) ⇒ **it only conducts below V_cell ≈ 3.35 V**. Measured on build #1 2026-09-27: plugging the 15 V brick with a cell above that does nothing at all; the only release is a manual short. ⚠ **Build #1's workaround is tweezers across `U4` pin 1 ↔ pin 3 at every insertion** (§12.0.17) — acceptable on a bench, not in a wooden box in a bedroom, and this is a *user-replaceable* cell (README §10). ⚠ On the `-KB`: verify against its own datasheet that "Auto overdischarge recovery" actually covers the first-connection state before committing — §11.3 describes it for the *overdischarge* status and §11.1 does not name which status it means. Its `V_DL` is also 2.40 V vs 2.90 V, and its standby draw 2 µA vs 0.1 µA. The switch is the option that does not depend on reading a vendor's intent. Encoded as check `V17` |
| V18 | **[MUST] Movement = X40.879.NS (a.k.a. X40.879B), not X40.879** — BOM/procurement only; `M1`'s footprint, symbol and nets are unchanged, only its value field | one BOM line | The plain X40.879 is the **X27 with the 315° internal stop** (`SP-X27-e-C` table row 4). Build #1's movement buzzed without turning at the stop and ran again when reversed (2026-09-27). `datasheet/README.md` §4 had said "buy the no-stop variant" since v0.7; the locked BOM never carried it. ⚠ The `.NS` is sold by dashboard-repair suppliers, not DigiKey, and has no datasheet on file: **check pin pitch and body against `Juken_X40-879_DualShaft` before soldering it**. Not in `review_check.py` — the value field is a label, not something the gate can measure. **Build #1 keeps its plain X40.879 with the stop removed by hand (2026-09-27)** |

> ⚠ **V9's arithmetic, corrected 2026-09-22 — read V14, V15 and V16 with it.** V9 and V10 both
> divide `V_DIP` by **R_DS of the FET pair**. The board does not sense the FET pair; it senses
> `VSS`→`CS`, which on rev0.3 is the pair **plus 111 mΩ of 0.25 mm trace plus the TCO**. Every
> current figure in V9, V10 and V11 is therefore optimistic by 3.5–5× on rev0.3 silicon — V9's
> "3.7 A startup → 122 mV" is really 420–535 mV, and "charge 1 A → 33 mV" is really 113–145 mV.
> **V9 + V14 + V15 together make those numbers true**; none of the three is sufficient alone,
> and V9 is the only one of them a respin cannot simply delete. V10's `-HB` consequently drops
> from "V9 REQUIRES V10, they are one change" to a genuine [SHOULD]: with V14 + V15 a `-GB`
> clears the 3.7 A startup at 122 mV vs its 125 mV floor — still tight, so the `-HB`'s extra
> 50 mV is worth having when V11 can source it.

**Not for v0.4, deliberately:** the I²C probe timeouts (§12.0.4) are a `i2c_master_probe`
artifact, not a board problem — 100 addressed reads of a known register came back exact with
zero timeouts. Nothing to change in hardware.

---

## Status overview

**Legend** — ☑ done · ⏳ open · ⏸ deferred (accepted risk, revisit later) · ✔ accepted (no change)

### ☑ Fixed

| # | Finding | Fixed in | Note |
|---|---|---|---|
| 1 | Q4 PVDD-mux P-FET source/drain reversed | `1f3736a` | schematic only — **PCB re-route still open** |
| 2 | TAS5760M PBTL outputs paralleled wrong pairs | `1f3736a`, refined `1cf1629` | schematic only — **PCB re-route still open** |
| 3 | LT3652 `C104` → 26 min charge timeout | `1f3736a` | 1 µF, same 0603 land, existing BOM line |
| 10 | J7/J10 identical connectors, incompatible pinouts | `637be57` | connector kept; **`SENSOR` + `KNOB` silkscreen added** on B.SilkS. **Re-opened and closed again 2026-08-08**: a 1×07 J7, which would have made the mis-mate physically impossible, was proposed in `kicad-sensor/REVIEW.md` and **rejected** — a footprint swap on both boards plus re-routing J7's fan-out here, for a connector plugged once at build time inside a sealed box. **The silk is the keying**; label both harnesses to match it |
| 11 | J7 pin 6 (`ALS_INT`) was NC | `727dbfd` | → expander GPB3; **PCB trace still open** |
| 12 | J7 value string said LIS3DH | `727dbfd` sch · `3cc15da` fw | schematic **and** `FIRMWARE.md` now say BNO085 — see note below |
| 13 | `R1` 137 mW in a 100 mW 0603 | `637be57` | → **1206**, `RC1206FR-071KL` (¼ W); **PCB land swap still open** |
| 15 | `VBAT_SENSE` floats above +3V3 | `727dbfd` | **D14** added; **PCB place + route still open** |
| 17 | Encoder divider 66.7 kΩ source impedance | `727dbfd` | → 10k/20k, same ratio, value-only |
| 20 | Reverse-cell fault current into the protector | `637be57` | `R20` 100R → **200R** (HYCON's max), halves it to ~18 mA |
| 19 | PVDD bulk under-rated for ripple | `35ca174` | → hybrid polymer, same D6.3 land: **BOM-only, no PCB impact**. **MPN corrected 2026-08-10** — `EEH-ZA1E101P` → **`EEH-ZA1E101XP`** (the typo'd number does not exist; PCBWay could not quote it). Stock verified: LCSC C264047 / DigiKey 3088115 |
| 21 | MCP23017 INTA/INTB tied | `637be57` | firmware requirement **R-BOARD-1** in `FIRMWARE.md` §6.5 |
| — | `FIRMWARE.md` sensor was LIS3DH, board is BNO085 | `3cc15da` | new §6.5.1 + **R-BOARD-3**; `SENSOR_INT` is BNO085-only now that `ALS_INT` is on GPB3 |

> ✅ **#12's firmware consequence is now handled.** `FIRMWARE.md` had specified an
> **LIS3DH @ 0x18** throughout. Corrected to **BNO085 @ 0x4A** in `3cc15da`, including a new
> §6.5.1 covering what actually changes: SHTP/SH-2 transport instead of a register map,
> `SENSOR_INT` meaning "packet available" rather than "tap happened", asynchronous boot,
> enabling only `SH2_TAP_DETECTOR`, clock stretching, and **R-BOARD-3** — `NRST` has no host
> line, so firmware cannot reset the hub and must degrade gracefully instead.

### 🔌 PCB sync — done 2026-08-04 (`4f00d68`)

The board was one part, one footprint, seven values and eleven pad-nets behind the
schematic. `gen/sync_pcb.py` closed that gap:

| | applied |
|---|---|
| New part | **D14** (BAT42W, SOD-123) placed at (76.50, 80.00) B.Cu |
| Footprint | **R1** 0603 → **1206** (position/rotation/side/nets preserved) |
| Values | `C104` 1µF · `R20` 200R · `R111`/`R112` 10k · `R114`/`R115` 20k · `J7` label |
| Pad nets | 11 — Q4.2/Q4.3 swap, U9.20/23/26, C181.2/C182.2/C183.2, L6.1, new `ALS_INT` on J7.6 + U13.4 |
| Copper cut | 11 stubs that would have shorted two nets, + 11 stale fragments |
| Zones | refilled (headless `ZONE_FILLER` **works** in KiCad 10 — `PCB_NOTES.md` was out of date) |

**Verification:** schematic ↔ PCB now agree on every part, footprint, value and pad
net (0 mismatches). DRC: **0 errors**, 7 warnings, **12 unconnected**.

D14's placement was chosen against **courtyards, tracks and vias** — a first pass
that only checked pad bounding boxes put it inside J3's courtyard and on top of a
`CELL_TEST` track. The chosen slot is 0.9 mm from `VBAT_SENSE` copper and 7.6 mm
from `+3V3` (it carries a few µA, so the longer leg is free).

**The 12 unconnected are the routing work**, and they are the whole of it:

| net | connection |
|---|---|
| `+5V` | Q4.3 → +5V (had to hop on F.Cu: Q4 pads 1/2 leave a 0.43 mm gap and a 0.25 mm track needs 0.45) |
| `PVDD` | Q4.2 → PVDD |
| `Net-(U9-SPK_OUTA+)` | U9.26 → leg A · C181.2 → leg A · C180.2 → leg A |
| `Net-(U9-SPK_OUTB+)` | U9.20 ↔ U9.23 · C182.2 · C183.2 · L6.1 |
| `+3V3` / `VBAT_SENSE` | D14 both ends |
| `ALS_INT` | J7.6 → U13.4 |

7 remaining warnings, all cosmetic and for the routing/silk pass: 3 dangling vias on
the old audio nets (they get consumed when those legs are re-routed) and 4 silkscreen
collisions introduced by the two new/changed footprints (D14 vs C131's reference,
R1's reference vs J1's shield pad).

### 🛣 Routing — done 2026-08-04 (`f480ced`)

All 12 ratsnest connections are routed. **DRC: 0 errors, 0 unconnected**, 4 silkscreen
warnings (cosmetic, see below).

| connection | how |
|---|---|
| `Q4.3` → `+5V` | B.Cu stub + **F.Cu hop** (vias at 100.92,70.16 and 97.61,68.26) — B.Cu cannot pass between Q4 pads 1/2 (0.43 mm gap vs 0.45 mm needed) |
| `Q4.2` → `PVDD` | direct B.Cu |
| `D14` → `VBAT_SENSE` | B.Cu + via onto the In1 run |
| `D14` → `+3V3` | B.Cu stub + F.Cu across + via |
| `ALS_INT` J7.6 → U13.4 | B.Cu in the 0.65 mm GPB lane, exiting to F.Cu before FULLCHG_EN's diagonal |
| leg A ×3, leg B ×4 | escape vias + F.Cu (the only free layer in that 46 mm² box) |

**The old leg-B trunk was recovered rather than re-routed.** After the net swap it survived
as *orphaned* copper on `Net-(U9-SPK_OUTA-)` (4 segs, 3 vias, U9.23→In2→In1→L6.1) — exactly
the path new leg B needed. Re-netting it to `Net-(U9-SPK_OUTB+)` and restoring three cut
stubs did most of leg B for free.

Also swept **350 zero-length track segments** (336 on `+5V`) that had been in the board since
the autorouter run in `91c5087` — 19 % of all segments, carrying no connectivity.

Three things the clearance checker had to learn, each caught by DRC disagreeing with it:
`pad.GetLayer()` lies for flipped pads · pads must be modelled as **rectangles** (a
circumscribed circle round U9's 1.90 × 0.40 pads on 0.65 mm pitch swallows both neighbouring
lanes) · **U9 carries a local clearance override of 0.2 mm**, twice the board rule.

Remaining 4 warnings are all silkscreen around D14, which landed in the tight
C131/C180-C183 cluster: its reference field and outline overlap C131's reference. Cosmetic —
for the silk pass, alongside the `#24` crystal-cap move.

### 🔥 Thermal vias (#5) — done 2026-08-04 (`c8dcf86`)

**49 GND vias added** inside the three exposed pads. DRC 0 errors / 0 warnings /
0 unconnected. Vias are tented (board setting), so solder cannot drain through during
hand assembly.

| part | EP | vias | ≈ via thermal path | dissipation |
|---|---|---|---|---|
| **U7** TPS55340 (12 V boost) | 3.4 × 5.0 mm | **14** | ~12 K/W | ~2 W at 12 W out |
| **U9** TAS5760M (amp) | 5.2 × 11 mm | **33** | ~5 K/W | ~1.5 W at 10 W out |
| **U2** LT3652 (charger) | 1.65 × 2.85 mm | **2** | ~84 K/W | ~0.7 W at 1 A |

(0.3 mm drill through 1.6 mm FR4 ≈ 169 K/W each, in parallel — indicative, not a
substitute for a thermal sim. Previously all three had **zero**, so the EPs could only
spread heat sideways through 35 µm of B.Cu.)

**U2 is the exception and it is finding #18's fault.** Its pad is 1.65 mm wide and two
inner-layer *signals* cross it: `Net-(U8-IO11_LRCLK)` runs vertically on In1 at x = 95.94,
right through the pad, and `+5V` closes the right side on In2. That leaves one usable
corner, hence 2 vias instead of the 4-6 the pad would otherwise take. **Rerouting those two
inner-layer traces clear of the pad is the fix**, and it is worth doing if `R18` is ever
changed to 2 A (#7), which roughly doubles U2's dissipation to ~1.4 W.

A checker bug is worth recording: an exposed pad's **paste-mask apertures are separate pads
with no copper layer**, and treating them as copper falsely blocked most of every EP —
U7 went 6 → 14 and U9 20 → 33 once they were excluded. U2 went 0 → 2 for the same reason.

### ⏳ Open — PCB / fab work (deferred to the routing pass)

| # | Finding | Sev | What it needs |
|---|---|---|---|
| ~~1, 2, 11, 15~~ | PCB side of the fixes above | ✅ | **done** — synced and routed, 0 errors / 0 unconnected |
| 4 | Power widths — **mostly done** | 🟠 | `POWER` net class + widening + **4 trunks moved to F.Cu** (*Fixed in a0031c9*); **`+3V3` widened 2026-08-06** (837 → 555 mΩ, ESP32 feed 258 → **169 mΩ**). **`VBAT` is the remainder**: 99.7 mm still ≤0.3 mm and in-place widening is exhausted — **re-verified 2026-08-06**, every thin segment on every power net has ≤0.10 mm of headroom and the three worst (21.5/14.9/6.7 mm on In2) have **0.00**. Needs hand re-routing, not a width change — see below |
| ~~5~~ | Thermal vias | ✅ | **done** — 49 GND vias: U7 **14**, U9 **33**, U2 **2**. U2 is capped by #18; **re-verified 2026-08-06 with the paste-aperture bug fixed: exactly 0 free 0.6/0.3 slots remain inside U2's EP**, so 2 is the honest maximum until #18 moves. Fine at `R18` = 1 A (~0.7 W); revisit if `R18` goes to 2 A |
| 8 | Switcher hot loops — **ground return done, placement not** | 🟠 | **Return half fixed** (*Fixed in `f55b15f`*): 23 vias tie every hot-loop return pad into the GND planes, 7.64 mm worst case → 0.62–2.20 mm. **Placement half needs pcbnew by hand** — every candidate slot for `C100`/`C102`/`C127`/`C128`/`C130`–`C132` fails routing or DRC; measured target coordinates are in §8 |
| ~~9~~ | `C238` 50 mm from U15 | ✅ | **done** (*Fixed in `8441d29`*) — moved to (26.73, 46.18); pad 1 → U15 pin 5 now **1.75 mm** (was 50.50), plus 2 GND vias 0.62 mm from its return pad |
| 18 | ~3 m of signal routing on the inner GND planes | 🟡 | **power copper on In1/In2 halved, 299.6 → 160.9 mm** (*Fixed in a0031c9*) — the four longest slots are gone. Signal routing on the inner layers is untouched, and still **blocks #5**: two inner-layer signals cross U2's exposed pad, capping it at 2 thermal vias instead of 4-6 |
| ~~25~~ | `AN-JST-001` (Juken mounting app-note) not on file | ✅ | **Closed 2026-08-08 — the footprint was validated against the vendor drawing by the board owner.** The 3× Ø3.0 mm peg holes and Ø4.6 mm shaft hole are confirmed, so the app note is no longer a gate. It remains the reference for **insertion force** and for snap-peg length vs board thickness, so re-open this if the 1.6 mm stackup is ever changed |
| ~~23~~ | U9 exposed-pad land vs TI drawing | ✅ | **checked 2026-08-06 against DAP0032C sheet 4223691/A.** EP copper **5.2 × 11 mm = TI exactly**. Pin lands 1.90 × 0.40 vs TI's 1.50 × 0.45 — an IPC-7351 alternate, which TI's note 6 permits, and the extra toe/heel + wider gap is *better* for hand soldering. **The one deviation is the mask/paste window: 4.11 × 4.36 mm vs TI's SMD-defined 3.04 × 3.74** (≈58 % more area). **Reviewed and confirmed correct by the board owner 2026-08-06 — no change.** See the pre-fab audit below |
| ~~—~~ | PCB had no title block | ✅ | **fixed 2026-08-06** — gerbers carried no title/rev/company/date. Now `rev "0.3"`, matching the schematic and the silkscreen. The old "title block reads rev A" finding was **wrong and has been withdrawn** |
| 26 | `R1` pad 2 hung on a 0.049 mm sliver | ✅ | **found and fixed 2026-08-06** — latent open left by the #13 0603→1206 land swap. See the pre-fab audit below |
| 24 | 32.768 kHz load caps 5.9 mm from Y1 | 🟡 | **placement done** (*Fixed in `3d6d830`*) — `C145` 5.85 → **2.60 mm**, `C146` 5.85 → **1.75 mm**; XTAL_P 9.1 → 5.46 mm, XTAL_N 14.0 → 4.95 mm, B.Cu only, 0 vias, 4 GND vias ringing the pair. Items 2–4 of the recommendation (keep the ABS07, first-article check, FW fallback) still stand |

### 🔩 Mechanical: hole density and board thickness — assessed 2026-08-04

**The holes are not a fragility problem.** Every hole on the board, of every kind:

| | area | % of board |
|---|---|---|
| 615 vias (all 0.3 mm) | 43.5 mm² | 0.36 % |
| 54 plated through-holes | 70.5 mm² | 0.58 % |
| 9 non-plated (motor shaft/pegs, holder, USB) | 62.1 mm² | 0.51 % |
| **total** | **176 mm²** | **1.46 %** of 12 069 mm² |

Locally, inside the exposed pads where the new vias went, hole area is **U7 5.8 %,
U9 4.1 %, U2 3.0 %** of the pad — ordinary for a PowerPAD via array, and the pads are
small islands inside a continuous board. Stiffness is set by the laminate that is still
there; 1.5 % perforation, spread out, does not measurably change it. **No reason to remove
or thin the arrays.**

**What actually governs robustness here is the mounting, not the thickness.** The board is
110 × 110 mm with **four corner M3 holes only** (5,5 · 104.8,5.2 · 5,105 · 105.5,105.5), and
the 18650 holder sits at (51, 96) — **47 mm from the nearest mount**, in the middle of an
unsupported bottom edge. Inserting a cell into a sprung holder is the largest force this
board will ever see in normal use, and it lands exactly there.

Going 1.6 → 2.0 mm buys stiffness ∝ t³ = **1.95×**. A fifth mounting hole near (55, 100)
would have cut that span roughly in half (deflection ∝ span³, so ~8× on the mode that
matters) — **considered and declined 2026-08-04: the board keeps its four corner mounts.**
Thickness is therefore the only lever left on this axis.

**If you do go to 2.0 mm, three things need checking first:**

1. **Aspect ratio.** The smallest drill on the board is **0.2 mm** (the ESP32 module's
   12-hole thermal array). At 1.6 mm that is 8:1; at 2.0 mm it becomes **10:1**, which is at
   or past most fabs' standard limit and moves the order into a premium tier. The 0.3 mm
   vias are fine either way (5.3:1 → 6.7:1).
2. **The Juken motor's snap pegs.** X27 §3.2/§3.4 defer hole sizes and insertion force to
   application note **AN-JST-001, which is not in `datasheet/`** (finding #25). The *hole
   sizes* were validated against the vendor drawing on 2026-08-08 and are settled — but
   snap pegs are moulded for a specific board thickness, and the note is still the only
   source for **insertion force** and peg length. At 1.6 mm this is closed; **a thickness
   change re-opens it**, and it is the one change that could stop the motor seating at all.
3. **Through-hole connector retention** — J1's USB-C shell pegs in particular. (BT1 is
   surface-mount, so the holder itself is unaffected.)

Thermally, 2.0 mm makes the new vias ~25 % worse (longer barrel), which is second-order
next to going from zero vias to 49.

### ⚡ Power widths (#4) — partially done 2026-08-05 (`a20faef`)

A `POWER` net class (1.0 mm track, 0.8/0.4 via, board-default 0.1 mm clearance) now covers
`VBAT`, `PVDD`, `+5V`, `+12V`, `VBUS` and both amp output legs, so future routing defaults
to copper instead of 0.25 mm. Every existing segment on those nets was then widened to the
most its own neighbourhood allows, per-net targets from IPC-2221 (1 oz, external, ~20 °C):

| net | total copper R | narrowest | still ≤0.3 mm |
|---|---|---|---|
| `VBAT` | 408 → **268 mΩ** (−34 %) | 0.25 mm | **48 %** of its length |
| `PVDD` | 118 → **77 mΩ** (−35 %) | 0.25 mm | **53 %** |
| `+5V` | 513 → **322 mΩ** (−37 %) | 0.25 mm | 36 % |
| `+12V` | 187 → **111 mΩ** (−41 %) | 0.25 mm | — |
| `VBUS` | 107 → **83 mΩ** (−22 %) | 0.25 mm | — |
| amp leg A / leg B | 58 → **40** / 56 → **33 mΩ** | 0.25 mm | — |

Point-to-point, where the path is pure track: charger BAT → cell+ **126 → 70 mΩ**,
12 V → wake LEDs **136 → 69 mΩ**, PVDD ORing → amp **61 → 47 mΩ**, 5 V → motor VM
**172 → 146 mΩ**.

**Read the "narrowest" column, not the average.** A net's current capacity is set by its
tightest neck, and every one of these still contains 0.25 mm segments — ~1.2 A at +20 °C,
against VBAT's 4 A and PVDD's 3 A peaks. **So #4 is not closed by this.** The resistance win
is real, the ampacity limit is not yet lifted.

The remaining necks are not scattered — they are a few long runs on the **inner layers**:

| net | worst neck | where |
|---|---|---|
| `+5V` | **57.1 mm** at 0.25 mm | In2.Cu, (20.5, 44.7) → (77.6, 44.7) |
| `VBAT` | **21.5 mm** at 0.25 mm | In2.Cu, (51.0, 61.0) → (72.5, 61.0) |
| `VBAT` | 11.9 mm | B.Cu, (86.0, 39.3) → (86.0, 51.2) |
| `PVDD` | 11.9 mm | B.Cu, (106.7, 71.3) → (106.7, 83.2) |

They cannot widen in place because In2 is packed with the signal routing of **#18**. The fix
is the one #4 always pointed at: **move these trunks onto F.Cu**, which is still ~98 % empty
(118 mm of track on the whole layer). That is a re-route, not a width change, and it closes
#4 and a good part of #18 together.

#### Trunks moved to F.Cu — 2026-08-05

Four of them, each getting a via cluster at both ends (parallel vias sized to the net's
peak current — one 0.4 mm via is good for ~1.5 A) and a short stub of the original inner
copper kept under the cluster so every via is tied on both sides:

| net | run | was | now |
|---|---|---|---|
| `+5V` | 57.1 mm, (20.5, 44.7) → (77.6, 44.7) | In2.Cu 0.25 mm | **F.Cu 1.00 mm**, offset −0.40 |
| `+12V` | 42.8 mm, (30.1, 76.5) → (72.9, 76.5) | In2.Cu 0.60 mm | **F.Cu 1.00 mm** |
| `+5V` | 23.9 mm, (76.7, 9.2) → (76.7, 33.0) | In1.Cu 0.60 mm | **F.Cu 1.00 mm** |
| `VBAT` | 27.9 mm, (103.4, 61.0) → (103.4, 88.8) | In1.Cu 0.50 mm | **F.Cu 0.97 mm**, offset −0.25 |

| | before | after |
|---|---|---|
| power copper on In1/In2 | 299.6 mm | **160.9 mm** (−46 %) |
| `+5V` ≤0.3 mm / R | 95.1 mm / 322 mΩ | **39.8 mm / 235 mΩ** |
| `+12V` R | 111 mΩ | **99 mΩ** |
| `VBAT` R | 268 mΩ | **260 mΩ** |
| DRC | 0/0/0 | **0/0/0** |

**`VBAT`'s necks survive, and this is where #4 stops being automatable.** 99.7 mm of VBAT is
still ≤0.3 mm (≈57 mm on B.Cu, ≈43 mm on In2), and a sweep of every thin power segment on
the board shows **≤0.05 mm of widening headroom on each** — the widening pass already took
everything the current placement offers. Three specific dead ends:

- **`VBAT` (51.0, 61.0) → (72.5, 61.0), 21.5 mm at 0.25 mm — the worst one.** Its east end
  sits inside M1's pad field. There are ~190 free via slots within 3.6 mm of it, but not one
  has a clear In2 jumper back to the node, so neither moving the trunk nor running a *parallel*
  F.Cu trunk beside it can be tapped at that end.
- **`VBAT` (35.6, 59.0) → (48.9, 59.0)** was left alone deliberately. It is already 0.50 mm,
  and shortening it to a stub puts its end 0.096 mm from an M1-2i diagonal — the full-length
  track clears, the stub does not. Nothing to gain, a DRC error to lose.
- The diagonal past (72.5, 61.0) is boxed in by GND copper and takes only 0.31 mm on F.Cu, so
  extending the chain buys a neck rather than removing one.

Closing the rest means **moving other nets out of the way by hand in pcbnew** — a placement
and re-route job around M1, not something the width/via passes can reach.

### 🔎 Pre-fab audit — 2026-08-06

A DFM/latent-defect sweep over the routed board, looking specifically for things
`kicad-cli drc` structurally cannot report. **Baseline: DRC 0 errors / 0 warnings /
0 unconnected, ERC 0, `review_check.py` 11/12 with 0 regressions, zone fills verified
current (a headless refill changes 0 of 4).**

#### 26. `R1` pad 2 was hanging on 0.049 mm of copper — FIXED

The one real defect found. `Net-(U1-VDD)` reached `R1` pad 2 through a **0.049 mm-wide
strip**, well inside any fab's etch tolerance:

| | |
|---|---|
| cause | the #13 0603 → 1206 land swap. The track ended at x = 98.675, dead centre of the **old** 0603 pad. The 1206 pad's outer edge sits at x = 98.600, so the centreline missed it by 0.075 mm and only the track's 0.125 mm end cap still overlapped |
| why DRC was silent | connectivity is a boolean. Any overlap ≥ 1 nm reads as connected — 0 unconnected items, no warning |
| what it would have done | `R1` feeds the CH224K's shunt-regulated VDD. Open it and there is no PD negotiation → no 15 V → no charging and no 12 V rail. A board that looks fine and doesn't work |
| fix | one added B.Cu segment, (98.675, 35.092) → the pad centre (98.037, 35.092). It lies entirely inside the pad plus the existing end cap, so **no copper exists anywhere it did not already exist** — DRC-neutral by construction |

**A full sweep for the same class of defect found nothing else.** Every pad on the board
and every free track end was scored on how much copper actually bridges the joint:
**0 pads and 0 track ends now below 0.12 mm** (was 1 and 1, both `R1`). Worth keeping as a
standing check — footprint swaps are exactly what produces these.

#### `+3V3` widened — the rail the #4 pass never covered

`+3V3` was never in the `POWER` net class, so `a20faef` skipped it and **100 % of its
423 mm was still 0.25 mm**, making it the highest-resistance rail on the board. Same
method as `a20faef` (width-only, no endpoint moves, no re-routing), capped at 0.80 mm on
the outer layers and 0.60 mm on In1/In2:

| from `L3` (3V3 buck out) to | before | after |
|---|---|---|
| **`U8` ESP32 3V3 pin** | 258 mΩ | **169 mΩ** |
| `U9` DVDD / AVDD | 569 / 512 mΩ | **393 / 346 mΩ** |
| `U13` MCP23017 | 405 mΩ | **273 mΩ** |
| `U11` motor driver VCC | 388 mΩ | **270 mΩ** |
| `J7` sensor board | 413 mΩ | **285 mΩ** |
| net total copper R | 837 mΩ | **555 mΩ** (−34 %) |

97 of 164 segments widened. The two that mattered were the **42.9 mm In2 run at y = 9.83
feeding the MCU (0.25 → 0.60)** and the **22.8 mm In1 run at x = 102.62 (0.25 → 0.60)**.
Only the MCU number has real headroom consequences: at a 500 mA Wi-Fi TX peak the DC droop
at U8's pin goes **129 mV → 85 mV** against 300 mV of margin to the 3.0 V floor. Everything
else on the rail draws single-digit mA and was never in trouble — the win there is noise
coupling, not droop.

Widening an inner-layer trace does not meaningfully worsen #18: **a slot's return-path cost
is set by its length, not its width**, and these slots already existed at full length.

**Two segments' worth of the pass had to be given back, and the reason is worth recording:
`U9` carries a local clearance override of 0.2 mm** — twice the board rule, the same trap
the `f480ced` routing pass hit. The width solver modelled the board default and produced 3
clearance errors plus 1 starved thermal on `C161`. All 12 `+3V3` segments within 2.5 mm of
a `U9` pad (and 2 near `C161`'s GND pad) were reset to 0.25 mm; DRC back to 0/0/0.

#### The 2026-08-06 manual edits, assessed

| edit | verdict |
|---|---|
| `Y1` reference moved to (0.885, −1.9) | fine, cosmetic |
| `PVDD` (102.68, 83.12)→(102.68, 81.63) redrawn | identical geometry, new UUID. No-op |
| **`VBAT` stub out of `Q2` pad 3 re-drawn as a 5-segment chain at 0.30 mm** (was one 0.96 mm diagonal at 0.25 mm) | path kept, **width reverted to 0.25 mm** — and the combination beats both originals |

At 0.30 mm the chain bought **~0.1 mΩ** (0.96 mm going 0.25 → 0.30 on a net that totals
261 mΩ) and cost **0.014 mm of clearance to `Q2` pad 2**: 0.1169 mm before → 0.1029 mm after,
the second-tightest gap on the board. `Q2` pad 2 is `Net-(BT1-Pin_1)`, the **raw cell
terminal** — the one pair where a short bypasses the reverse-polarity FET and defeats
`CELL_TEST`, i.e. exactly where the safety section says to assume the worst.

**Reverted to 0.25 mm on 2026-08-06, keeping the re-routed path.** That was the right pairing:
the kink walks the trace away from pad 2, so at 0.25 mm it clears by **0.150 mm** — better
than the widened chain (0.1029) *and* better than the straight diagonal it replaced (0.1169).
The re-route was worth doing; only the width was not. Two 15.5 µm segments remain in the
chain — router artefacts, harmless, left alone rather than risk re-drawing the path.

| `Q2` pad 2 ↔ `VBAT` | clearance |
|---|---|
| original straight diagonal, 0.25 mm | 0.1169 mm |
| re-routed chain, 0.30 mm | 0.1029 mm |
| **re-routed chain, 0.25 mm (now)** | **0.1500 mm** |

#### Fab risk, measured

| | value | verdict |
|---|---|---|
| DRC / ERC / unconnected | 0 / 0 / 0 | clean |
| min track | 0.25 mm | standard |
| clearance rule | 0.10 mm | **at the floor of a standard 4-layer process** |
| pairs at exactly 0.100 mm | **16** | no margin at those 16 spots — **unchanged by this session's edits** |
| pairs below 0.127 mm (5 mil) | **347** | fine at JLC/PCBWay standard, not at a 5-mil-only shop |
| min annular ring | 0.15 mm (0.3/0.6), 0.20 on the 0.4/0.8 power vias | standard |
| smallest drill | **0.20 mm ×12** (ESP32 EP array) → **8:1** aspect at 1.6 mm | at the standard-tier limit; **10:1 if the board goes to 2.0 mm** |
| min hole-to-hole (edge) | 0.274 mm | above the 0.25 rule, tight |
| min copper to board edge | 1.175 mm | comfortable |
| zone fills | current | gerbers will match the editor |

**Nothing here blocks fabrication.** The residual risk is not electrical — it is the three
items that have never been checked against a vendor drawing (#25 Juken `AN-JST-001`, the
Keystone 1043 footprint's own "VERIFY vs the drawing before fab" note, and the GCT USB-C
land) plus the two MPNs that still need a DigiKey stock check. Those are paperwork, and they
are the ones that scrap a whole board rather than cost a bodge wire.

> ### ✅ All three closed 2026-08-08
>
> **Validated against the vendor drawings by the board owner:** the **Juken
> X40.879** land (peg holes and shaft hole), the **Keystone 1043** holder
> (pegs, index post, PC-pin span — the footprint's own `VERIFY` note has been
> replaced with the verification), and the **GCT USB4160** USB-C land.
>
> That clears the whole "scraps a board" class. What is left before ordering is
> the two **stock** checks below (`R1` `RC1206FR-071KL`, `C172` `EEH-ZA1E101P`),
> which gate *assembly*, not bare-board fab — and neither board has been through
> a fab's DFM yet, since no Gerbers have been exported from either project.

#### Checked and found clean (no action)

- **Bypass-cap locality, board-wide.** Every 2-pad cap on `<rail, GND>` measured to its
  intended pin. The outliers are exactly the ones §8 already lists (`C161`/`C163` at
  10.2/11.7 mm from U9's DVDD/AVDD, `C140`/`C141` at 8.7/8.8 mm from U8) — the #9 sweep
  surfaced nothing new. `C142`/`C143` at 4.7/4.8 mm from U8's 3V3 pin is mediocre for an RF
  module but boxed in by the antenna keep-out and the crystal cluster.
- **Copper stubs.** One 1.05 mm dangling fragment existed, on `Net-(U1-VDD)` — it was the
  #26 track, now landed. Every other free end terminates on a pad, via, track or pour.
- **Courtyards.** 0 footprints missing one (the DRC config ignores `missing_courtyard`, so
  this was worth confirming independently).
- **Board outline.** 8 Edge.Cuts shapes, closed, 110 × 110 mm with R6 corners.
- **Li-ion labelling.** `BT1`'s footprint already carries `Li-ion 18650 only 2.5-4.2V` on
  silk, plus `CELL+`/`CELL-`. The safety-labelling requirement is met.
- **Exposed-pad zone connection.** All four GND pours use thermal relief (0.4 mm spokes,
  0.3 mm gap), including under U7/U9/U2's EPs. **Considered switching the EPs to a solid
  connection and declined**: the 49 vias already bond them to three full planes, so the
  extra B.Cu coupling is second-order, while a solid pour connection makes a PowerPAD
  materially harder to hand-solder — and hand-assembly is a hard project constraint.
- **`U1` (CH224K) EP has 1 via and room for ~15 more. Declined for the same reason** — it
  dissipates well under 0.15 W, so the only effect of via-in-pad there would be solder
  wicking on a part that does not need the heat path.

#### Revision stamping — settled 2026-08-06

**There was never a "rev A".** That claim, repeated twice in this document, was wrong:
`gen/build.py` has set `rev="0.3"` all along and the schematic title block reads
`(rev "0.3")`, matching the `Tibo - Wooden Clock v0.3` on F.Silkscreen. The two statements
below and in the schematic-readiness section have been corrected.

The real gap was the other file: **`clock.kicad_pcb` had no `title_block` at all**, so
gerbers and the fab drawing carried no title, revision, company or date. Added, matching
the schematic:

```
(title "Wooden Clock - main board") (rev "0.3") (company "Tibo") (date "2026-08-06")
```

The PCB's date is deliberately 2026-08-06, not the schematic's 2026-08-04 — the board
changed today and the schematic did not.

#### `U9` mask/paste window (#23) — closed 2026-08-06

Cross-checked against TI's drawing (above) and **confirmed correct by the board owner**;
no change. For the record, if a stencil is ever ordered: 7 of the 33 thermal vias sit
inside the current 4.11 × 4.36 mm aperture and will wick. Shrinking it to TI's
3.04 × 3.74 mm is a footprint-only edit that touches no copper. Hand-soldering the EP it
makes no difference, which is the build method that matters here.

### ⏸ Deferred — accepted for now, revisit later

| # | Finding | Why deferred | Revisit when |
|---|---|---|---|
| ~~6~~ **re-opened for build #1** | Protector OC trip | ⚠ **2026-08-10: PCBWay will supply `-GB` — LCSC C160793 (-HB) is out of stock.** On this build the finding is held closed by firmware (R-AUDIO-1's `-GB` budget), not by the part. ✅ **Fixed 2026-08-08 by part change: `HY2111-GB` → `HY2111-HB`.** Same SOT-23-6, same pinout, same support network, every threshold identical except discharge-OC `V_DIP` (200 ±25 mV vs 150 ±25 mV) — worst-case trip **1.89 A → 2.65 A**, which clears both the battery case and the plugged sunrise-alarm case. Speaker stays 4 Ω. Firmware side is `FIRMWARE.md` **R-AUDIO-1** | Only if the audio ceiling or the LED budget is raised |
| 7 | Battery IR drop / `R18` caps the wall at ~1 A | Still deferred. The **cell supplies the balance even while plugged**, which is why #6 mattered — now covered by the -HB trip with ~15 % margin on the sunrise-alarm case | `R18` 0.1 → 0.05 Ω doubles the wall's share, but needs thermal vias under U2 (#5, blocked by #18) |
| 14 | Ungated always-on loads (~70 mA idle) | **Mostly wall-powered**, so backup runtime is good enough | If battery runtime becomes a goal — gate the EM14 (26 mA) and QRE1113 LED (14 mA); GPA4-6/GPB3 are free |
| 16 | `CELL_TEST` on battery cuts power | Self-recovering reset loop, **not damage**; firmware-enforced instead | If a hardware interlock against `PD_PG` is ever wanted |

### 🧾 Schematic readiness — checked 2026-08-04 (`35ca174`)

The schematic is **complete and validated for the PCB phase.** Evidence, not assertion:

| Check | Result |
|---|---|
| `kicad-cli sch erc --severity-all` | **0 violations** |
| Generator lint (dangling wires, wires through bodies) | **clean** |
| Components / nets | 183 / 149 |
| Parts missing a footprint | **0** |
| Parts missing MPN / Manufacturer / Package | **0** (`stamp_bom`: 183 matched, 0 unmatched) |
| Unintentional dangling (1-pin) nets | **0** — all 18 are explicit NC flags, each verified deliberate |
| `review_check.py` schematic items | **8/8 pass, 0 regressions** |
| Remaining open findings that touch the schematic | **none** — every one is PCB, BOM-sourcing, or explicitly deferred |

The 18 deliberate no-connects: J1 SBU1/2 (USB 2.0 subset) · J6 DET_A/B (no spare GPIO for
card-detect) · U1 CFG2/3 (correct for CH224K single-resistor mode, WCH fig. 6.1) · U10 STAT ·
U13 GPA4-7 spare + 2 NC pins · U16 VBUS (deliberate — the 15 V PD rail exceeds the pin's
5.25 V rating) · U3 NC · U8 IO35-37 (reserved by the octal PSRAM).

**Delta the PCB must absorb (what F8 will reconcile):**

| Kind | Items |
|---|---|
| New part | `D14` (BAT42W, SOD-123) — place near D13 |
| Footprint change | `R1` 0603 → **1206** |
| Value changes | `C104` 100nF→1µF · `R20` 100R→200R · `R111`/`R112` 100k→10k · `R114`/`R115` 200k→20k · `J7` label |
| Net changes | Q4 pads 2/3 · U9 pads 20/26 · C181/C182 far pads · new `ALS_INT` |

**Two things that are not blockers but are decisions you own:**

1. ~~**Revision letter.**~~ **Withdrawn 2026-08-06 — this finding was simply wrong.** The
   title block never read "rev A"; `gen/build.py` sets `rev="0.3"` and the schematic has
   carried `(rev "0.3")` throughout, consistent with the silkscreen. The genuine gap was that
   the *PCB* had no title block; that is now fixed. See the pre-fab audit above.
2. ~~**Two MPNs need a DigiKey stock check** before ordering~~ — **both closed 2026-08-10 by the
   PCBWay quote.** `R1` = `RC1206FR-071KL` (#13) quoted and sourceable at $0.441. `C172` was the
   one that bit: `EEH-ZA1E101P` (#19) **is not a real MPN** and PCBWay could not buy it —
   corrected to **`EEH-ZA1E101XP`**, in stock at both LCSC (C264047) and DigiKey (3088115).
   The written substitution rule in `parts_db.py` is what made the swap checkable in minutes.

### ✔ Accepted — no change planned

| # | Finding | Rationale |
|---|---|---|
| 22 | No UART console (IO43/44 consumed) | Known and accepted; USB-Serial-JTAG is the bring-up path, boot-log TX still probeable on IO43 |

### 🏭 Assembly quote — PCBWay `T-1N10W1120006A`, 1 unit (2026-08-10)

First real fab/assembly quote off this BOM (183 lines, $259.20 all-in: parts $146.83 + assembly
$29.00 + PCB $83.37). Six lines came back flagged. What they cost the design:

| item | ref | PCBWay said | answer |
|---|---|---|---|
| 14 | `C172` | "provide exact part number or URL" | **Our MPN was wrong.** `EEH-ZA1E101P` is not a real part — the ZA series uses the plain `-P` suffix only at other voltages/values (`EEH-ZA1H101P` = 50 V, `EEH-ZA1E560P` = 56 µF); the 25 V/100 µF part is **`EEH-ZA1E101XP`**. Corrected in `parts_db.py` + stamped into both files. LCSC **C264047** (4,252 stk) / DigiKey **3088115** (3,364 stk). Same land, 2 A @100 kHz, 30 mΩ — #19's rule is met 3× |
| 22 | `D40`/`D41` | "1 = 10 pack" | Adafruit **2758** confirmed (natural white ~4500 K). Asked them to **ship the 8 unused pixels** — 5 of them are the off-board status row on `J12`, which is not a BOM line |
| 23 | `F1` | `[DNP]` | **Accepted, and correct**: a 77 °C one-shot TCO cannot survive reflow. ⚠ **The safety chain is therefore incomplete as delivered** — see below |
| 36 | `L4` | price rising | accepted at actual price |
| 37 | `M1` | `[DNP]` | as instructed; holes must stay |
| 75 | `U3` | "we will supply `HY2111-GB`" | **-HB is out of stock at LCSC (C160793)**, and our own BOM note handed them C82747, which *is* the -GB. -HB requested if they can source it, **-GB accepted otherwise** — which un-does #6, see below |

**Two consequences that outlive the order:**

1. **`F1` ships unpopulated.** The board must not be run with a cell in the holder until the
   Cantherm `SDF-DF077S` is hand-soldered in (≥3 mm from the body, heatsink the lead). DigiKey
   1014754, $0.87, 6,508 in stock. Until then the cell's only thermal backstop is `RT1` + the
   LT3652's NTC qualification, which covers *charging* and not a cell that goes hot on its own.
2. **`U3` is a `-GB` again unless PCBWay finds -HB.** #6 was closed by that part change; on this
   build it is closed *by firmware instead*. Worst-case discharge-OC trip goes back to
   **1.89 A** (150 ±25 mV / 50–66 mΩ), and the plugged sunrise-alarm case draws **~2.3 A from
   the cell** — i.e. it trips. **`FIRMWARE.md` R-AUDIO-1 now carries a `-GB` budget** (keep peak
   cell current < ~1.8 A: full 8 W audio *or* the LED ramp, never both). **Check the marking on
   the assembled board** and relax the budget only if it reads -HB.

---
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
