tibm/clock/kicad/3d/FH34SRJ-10S-0.5SH.stp

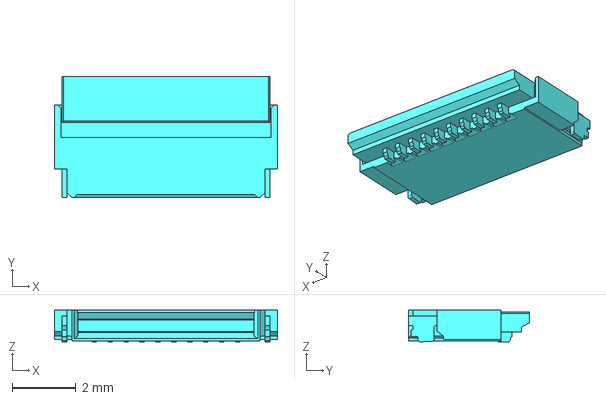
[picture p15: CAD file, 2026-07-18]
kicad/3d/FH34SRJ-10S-0.5SH.stp
7.00 x 3.80 x 1.00 mm
