tibm/clock/cad/switch.stp

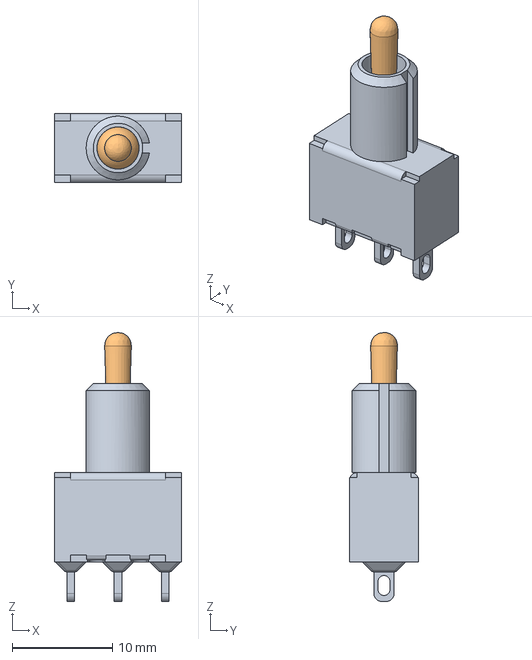
[picture p16: CAD file, 2026-08-07]
cad/switch.stp
12.7 x 6.86 x 26.8 mm
