tibm/clock/firmware/components/services/include/clk/services/motion.hpp

// The movement.                                               [FIRMWARE.md §6.1, D5, D7]
//
// Owns both axes of the X40.879 and the homing opto.  Nobody else touches hal::motor.
//
// What lives here is the part that carries the bugs: the trapezoidal profile, the backlash
// policy, and the homing FSM.  What does NOT live here is commutation -- the HAL is a
// velocity-controlled step generator with a stop target (see hal::motor), so this file is
// the same on the bench and in clocksim.
#pragma once

#include <cstdint>

#include "clk/ao.hpp"
#include "clk/hal/hal.hpp"
#include "clk/port.hpp"

namespace clk::svc {

class Motion final : public ActiveObject {
public:
    enum class State : uint8_t { Uninit, Homing, Idle, Moving, Fault };

    // Everything a bench session wants to change without a rebuild.  `motion tune` writes
    // these; they become NVS-backed config with `storage` (§7.5).
    struct Tuning {
        // Scaled by 2/3 on 2026-09-27 with kUstepsPerRev 17280 -> 11520: same deg/s as before.
        int32_t v_max = 4000;   // usteps/s  -- ~20 min of dial per second (125 deg/s)
        int32_t accel = 13333;  // usteps/s^2
        // Homing is two-speed.  The coarse sweep only has to notice that it crossed the
        // index, so it can run fast; the slow re-approach is what fixes the position.  Keep
        // v_coarse below about (window / 3) per control tick or the sweep steps over the
        // 3-degree window entirely -- which is a real bench failure, not a fake artefact.
        int32_t v_coarse = 2667;
        int32_t v_fine = 267;
        int32_t backlash = 0;  // usteps of slop to take up; every move finishes clockwise
        float opto_thresh = 0.45f;
        // ---- the per-unit calibration, one number per hand (`motion zero`, NVS-backed) ----
        //
        // The opto answers "the index mark is over the window", not "the hand is due north",
        // and the two differ by however the mark was printed, the hand pressed on and the
        // sensor soldered.  So each hand carries a trim in microsteps, POSITIVE = push the
        // hand clockwise, applied where the two frames actually meet: homing adopts
        // `-zero` at the index instead of 0, so asking for 12:00 afterwards lands on north.
        //
        // Written by set_zero() ONLY -- set_tuning() leaves them alone, because changing the
        // zero has to move the hands and shift every target with them, which is a thing the
        // AO does rather than a field a caller may assign.  Per unit, by hand, once.
        int32_t zero_h = 0;
        int32_t zero_m = 0;
        // Auto-home (§6.1): trim the hands from index crossings that happen anyway.  On, and
        // the switch is here because there are two times you want it off -- while measuring
        // the very error it corrects, and in a test that teleports the hands and does not
        // want the movement quietly noticing.
        bool autohome = true;
        // Level to gravity (§6.1d): let the dial re-reference its 12 to whichever of the
        // twelve dots is at the top.  On.  Off is for the bench -- measuring a zero or a
        // backlash with the hands free to jump thirty degrees mid-measurement is not a
        // measurement -- and it leaves the printed 12 as the 12, which is where it was.
        bool level = true;
    };

    struct Snapshot {
        State state;
        const char* state_name;
        const char* phase;  // homing sub-state, "" otherwise
        int32_t hour, minute;
        int32_t target_hour, target_minute;
        bool homed;
        bool powered;
        uint32_t home_ms;  // how long the last home took, sim ms
        float opto;
        uint32_t faults;
        int32_t zero_h, zero_m;  // the per-unit trim, as `motion zero` last left it
        uint32_t trims;          // index crossings that corrected the hands (§6.1 auto-home)
        int32_t last_trim;       // ... and by how much the last one did, usteps, signed
        uint8_t dial_tick;       // which dot is at the top, 0..11 (§6.1d); 0 = the printed 12
        int32_t dial_off;        // ... the same thing in usteps, added to every target
    };

    Motion() noexcept;

    // ---- asking the movement for something ------------------------------------------------
    //
    // Every one of these POSTS -- they are called from other threads and the AO owns the state
    // -- and every one of them RETURNS what the movement is going to do with it.  The return is
    // the whole point and it was missing: `motion step` called nudge(), got void back, and
    // printed a success line while the layer below dropped the target on the floor.  Two layers
    // below could refuse and neither could say so (FIRMWARE.md §12.2 F0.1).
    //
    // The Status is a synchronous verdict on the gates that are knowable here -- presence, the
    // NVS bench inhibit, and whichever state the FSM is in -- and it is advisory in the way any
    // check-then-act is: the FSM could move on between the answer and the event arriving.  On a
    // bench, where these are typed one at a time, that is the difference between a command that
    // lies and one that does not.  The post happens either way, deliberately: `want_` has to
    // record what was asked for even when it is held, because finish_home() re-issues it.
    //
    // `dir` is how to get there when the hand is not already on it.  0 takes the shortest way
    // round, which is what the CLOCK wants -- it follows a value that moves a minute at a
    // time, and 11:59 -> 12:00 is one minute forward however you write it down.  +1/-1 say
    // which way the KNOB is turning, and are also accumulated rather than taken flat: see
    // Motion::resolve.  Absolute microsteps; there is no "step N times" in this system (§6.1).
    Status goto_usteps(int32_t hour, int32_t minute, bool preview = false, int dir = 0) noexcept;
    // Bench only: `motion step`.  RAW and relative, and the one request that still works in
    // `Fault` -- see accepts().
    Status nudge(hal::motor::Hand, int32_t usteps) noexcept;
    Status home() noexcept;
    Status halt() noexcept;

    // What the movement would do with a request, right now.  `raw` distinguishes a bench nudge
    // from a dial-frame target, because they are refused by different gates:
    //
    //   NotPresent  no movement fitted (board.hpp's mask)
    //   Denied      the NVS bench inhibit -- `motion power on`, NOT `unsafe on` (F0.2)
    //   Busy        a homing run is using both shafts
    //   NotReady    the FSM is in `Fault`, and only a dial-frame target is refused for it:
    //               `motion step` is how the index mark gets placed, and a board that has
    //               never had one faults its boot home EVERY time.  Refusing the one command
    //               that can break that circle is what made the board unusable on the bench.
    [[nodiscard]] Status accepts(bool raw) const noexcept;

    // The per-unit trim, in microsteps, positive = clockwise (`motion zero`).  Posts, because
    // it is not a setting but a change of frame: the hand moves to it, every pending target
    // moves with it, and the new value goes to NVS.  Takes effect at the next home if the
    // movement has never found its index.
    void set_zero(hal::motor::Hand, int32_t usteps) noexcept;

    // Which of the twelve dots is at the top of the dial (§6.1d).  `ui` works this out from
    // gravity and posts it here, where the hands are; 0 is the cube upright and is what a
    // movement that has never heard from the sensor uses.  Also a change of frame -- but a
    // change of the DIAL's frame, not the movement's: it moves the hands and every pending
    // target and touches neither the zero nor the index, which stay bolted to the movement.
    void set_dial_tick(int tick) noexcept;

    // Whether to home as soon as the AO starts.  On by default -- the hands are wherever the
    // last power-off left them and nothing else can find out where that is (§6.1).  clocksim
    // turns it off for the test rig, where a nine-second sweep before every case buys
    // nothing; the case that tests boot homing turns it back on.
    void set_home_on_start(bool on) noexcept { home_on_start_ = on; }

    [[nodiscard]] Snapshot snapshot() const noexcept;
    [[nodiscard]] Tuning tuning() const noexcept;
    void set_tuning(Tuning const&) noexcept;  // ... except zero_h/zero_m -- see set_zero

    // Gets HandState on every settle and HomeDone when homing finishes.  One subscriber is
    // enough for now (chrono); a real bus lands with §3.5.
    void subscribe(ActiveObject* ao) noexcept { sub_ = ao; }

protected:
    void on_start() override;
    void on_event(Event const&) override;
    void on_tick() override;

private:
    // §6.1's sequence, with the two changes the first bench-less run argued for.
    //
    // `Clear` comes first because §6.1's version assumes the sensor starts dark: a hand
    // already parked on the index holds it lit, there is never a RISING edge to find, and
    // the whole run fails.  With both hands there it is not knowable which one is
    // responsible either -- so Clear does not guess.  It moves the hour hand 45° (fifteen
    // times the width of the window, sampled every tick of the way) and, if the sensor is
    // still lit after that, it has PROVED the hour hand was not the cause and moves the
    // minute hand instead.
    //
    // And each hand is found twice, fast then slow, rather than once slowly.  The coarse
    // pass only has to establish which revolution we are in; the fine pass is what sets the
    // zero.  That plus reusing the hour hand's now-known index (rather than sweeping a
    // second time for it) takes a homing run from ~35 s to ~9 s.
    //
    // HOUR first (2026-09-27): it is the near, bright hand and it occludes the minute hand,
    // so it is found first and then parked out of the way.  A hand whose search fails is
    // searched again from its coarse pass at half the speed, up to kHomeTries times in all --
    // on build #1 the minute hand's dip is ~9 mV deep and a fast sweep can step over it.
    enum class Phase : uint8_t {
        None,
        Clear,       // get BOTH hands off the sensor before trusting any edge
        CoarseHour,  // fast: which revolution is the index in?
        FineHour,    // slow re-approach: where exactly?
        ParkHour,    // a known, exact move well clear of the index
        CoarseMinute,
        FineMinute,
        Done,
    };

    struct Axis {
        hal::motor::Hand hand;
        int32_t target = 0;
        int32_t via = 0;   // backlash undershoot; == target when the move is already CW
        bool leg2 = true;  // false while still heading for `via`
        bool active = false;
        int32_t v = 0;
    };

    void plan(Axis&, int32_t target) noexcept;  // target: absolute, already resolved
    [[nodiscard]] int32_t resolve(int32_t prev, int32_t from, int32_t to, int dir) const noexcept;
    bool step_axis(Axis&, uint32_t dt_ms) noexcept;  // true while still moving
    // Ok, or what the driver said.  NotPresent is a legitimate answer and the caller decides
    // what it means -- for a homing run it means there is nothing to home (D16).
    Status power(bool on) noexcept;
    void publish() noexcept;
    void enter(Phase) noexcept;
    void run_homing(float opto) noexcept;
    void finish_home() noexcept;
    void fail(const char* why) noexcept;
    // Search the current hand again, slower -- or fail(why) once kHomeTries are spent.
    void retry_or_fail(hal::motor::Hand, const char* why) noexcept;
    [[nodiscard]] int32_t slowed(int32_t v) const noexcept { return v >> tries_; }
    // ---- the index, outside a homing run -------------------------------------------------
    // Where the index sits in a hand's own frame: `-zero`, because homing adopts it there.
    [[nodiscard]] int32_t index_pos(hal::motor::Hand) const noexcept;
    [[nodiscard]] Axis& axis_of(hal::motor::Hand) noexcept;
    // Auto-home: every crossing of the index is a free calibration, so watch for one whenever
    // we are NOT homing and correct the hand that made it.  Cheap, and it is the difference
    // between a clock that is right at boot and a clock that stays right.
    void watch_index(float opto) noexcept;
    void trim_hand(hal::motor::Hand, int32_t err) noexcept;
    // Shift one hand's whole coordinate frame by `d` usteps without moving it, and take every
    // pending target with it.  Both `motion zero` and an auto-home trim are this.
    void shift_frame(hal::motor::Hand, int32_t d) noexcept;
    void retarget() noexcept;  // re-plan both axes onto want_h_/want_m_ and go
    // How far to back off before a fine re-approach: three coarse samples' worth of travel,
    // because that is exactly how far past the index the coarse pass can have carried us.
    // It scales with the measured tick, so a warped simulation widens it automatically.
    [[nodiscard]] int32_t fine_backoff() const noexcept;

    [[nodiscard]] int32_t pos(hal::motor::Hand h) const noexcept {
        return hal::motor::state(h).pos;
    }

    mutable port::Mutex mx_;
    Snapshot snap_{};
    Tuning tune_{};

    Axis hour_{hal::motor::Hand::Hour};
    Axis min_{hal::motor::Hand::Minute};

    State state_ = State::Uninit;
    Phase phase_ = Phase::None;
    bool homed_ = false;
    bool powered_ = false;
    uint64_t idle_since_us_ = 0;
    uint64_t last_tick_us_ = 0;
    uint64_t home_start_us_ = 0;
    uint64_t phase_start_us_ = 0;
    float opto_ = 0.0f;
    bool opto_high_ = false;
    uint32_t dt_ms_ = 10;      // measured control period, in SIM time
    uint8_t clear_stage_ = 0;  // 0 = moving the hour hand off the mark, 1 = the minute
    bool clear_started_ = false;
    uint8_t fine_pass_ = 0;
    int32_t backoff_ = 0;
    uint8_t tries_ = 0;        // failed searches of the CURRENT hand; each halves both sweep speeds
    float sweep_peak_ = 0.0f;  // brightest opto this phase saw -- logged when a search fails
    uint32_t faults_ = 0;
    bool home_on_start_ = true;
    // Auto-home bookkeeping.  `lost_` counts index crossings that landed nowhere near where
    // they should have: one is noise or the other hand, three in a row is a movement that has
    // genuinely slipped, and the answer to that is a real home.
    uint32_t trims_ = 0;
    int32_t last_trim_ = 0;
    uint8_t lost_ = 0;
    // Where the dial's 12 currently is, in the movement's own microsteps (§6.1d).  Always a
    // multiple of kRev/12, always added to an incoming DIAL-frame target and never to a raw
    // one, and deliberately not persisted: it is a fact about the room, not about the unit.
    int32_t dial_off_ = 0;
    uint8_t dial_tick_ = 0;
    // The last target asked for, re-issued after a home completes: whatever the clock wanted
    // while the hands were busy finding zero is still what it wants afterwards.  For a
    // DIRECTED target this is also the setpoint each new one is accumulated onto, so it is
    // unwrapped and may be several revolutions away from the hand (see resolve()).
    int32_t want_h_ = 0, want_m_ = 0;
    bool want_valid_ = false;
    ActiveObject* sub_ = nullptr;
};

Motion& motion() noexcept;

}  // namespace clk::svc
