tibm/clock/firmware/components/clk_hal/host/src/hal_host.cpp

// Fake peripherals for clocksim and the host tests.        [FIRMWARE.md D14, §11.2]
//
// Fidelity rule (§13.9): model what the firmware LOGIC branches on, never the device's own
// physics.  So the opto has a dark/bright span and noise, because homing branches on a
// threshold -- but there is no phototransistor model, because nothing in the firmware can
// tell the difference and a wrong model is worse than no model.
#include <sys/stat.h>
#include <sys/statvfs.h>

#include <algorithm>
#include <chrono>
#include <cmath>
#include <cstdio>
#include <cstdlib>
#include <cstring>
#include <mutex>
#include <string>
#include <thread>
#include <vector>

#include "../../shared/sd_detail.hpp"
#include "clk/board.hpp"
#include "clk/hal/bme688.hpp"
#include "clk/hal/hal.hpp"
#include "clk/hal/host/models.hpp"
#include "clk/hal/host/sim.hpp"
#include "clk/hal/pcm.hpp"
#include "clk/hal/tas5760m.hpp"
#include "clk/hal/tone.hpp"
#include "clk/hal/tsl2591.hpp"
#include "clk/log.hpp"
#include "clk/port.hpp"

namespace clk::hal {
namespace {

// ---- calibration placeholders ----------------------------------------------------------
// Real numbers arrive at milestone 3 with a probe on the QRE1113.  The opto span lives in
// hal.hpp (`adc::kOptoClearMv`) and the SoC endpoints in its `power` namespace, so the fake and
// the target cannot disagree about either -- including about the opto's SENSE, which they did
// until rev0.3 was measured.  There were file-local aliases for the opto pair here; they were
// shadowed by the very names they aliased inside `namespace adc` and warned as unused.
constexpr uint16_t kVbatEmptyMv = power::kVbatEmptyMv;
constexpr uint16_t kVbatFullMv = power::kVbatFullMv;
// `Q2`'s body-diode drop -- what the tap falls by when CELL_TEST turns Q2 off and there is no
// cell holding the holder+ net up (kicad/gen/b_charger.py).  The real part is 300-400 mV.
constexpr uint16_t kQ2DiodeMv = 350;

// ---- the mechanism ---------------------------------------------------------------------
// Where the hands physically sit at power-on.  Deliberately NOT zero: if the commanded
// microstep and the visible angle agreed, `motion home` would be a no-op and the homing FSM
// would be tested by nothing at all.  `sim hand h 0` when a test wants determinism.
constexpr float kHourStartDeg = 100.0f;
constexpr float kMinuteStartDeg = 250.0f;

// The index mark on each hand's underside crossing the 3.5 mm window at r = 23.5 mm, due
// north.  Half-width plus a linear edge, so the FSM sees an EDGE rather than a step -- an
// edge is what it will get on the bench, and a step would let a sloppy detector pass here
// and fail there.  Off-index the dial still returns a little light.
constexpr float kIndexHalfDeg = 1.5f;
constexpr float kIndexEdgeDeg = 0.5f;
constexpr float kOptoDarkNorm = 0.08f;

// One shaft.  Position is integrated LAZILY: p = pos + vel*(now - t0), evaluated when
// somebody asks.  No thread, exact under `sim warp`, and `sim jump` moves the hands the way
// a real 30 s of slewing would.  `pos` is fractional on purpose -- re-basing it on every
// control tick while truncating to whole microsteps would shed ~0.5 ustep per tick, which at
// a 100 Hz tick and full speed is a degree per second of invented drift.
struct AxisSt {
    double pos = 0.0;      // microsteps
    double stop_at = 0.0;  // microsteps; motion ends here
    int32_t vel = 0;       // microsteps/s, signed, + = clockwise
    uint64_t t0_us = 0;
    float offset_deg = 0.0f;  // physical angle - commanded angle.  The unknown homing solves
};

struct State {
    // time
    double warp = 1.0;
    uint64_t sim_base_us = 0;
    uint64_t real_base_us = 0;
    // analog
    bool opto_auto = true;  // derive the opto from where the hands are; a write flips it off
    float opto = 0.10f;     // only consulted when opto_auto is false
    uint16_t vbat_mv = 4021;
    uint16_t noise_mv = 0;
    uint32_t rng = 0x1234'5678u;
    // knob
    int32_t count = 0;
    int32_t last_read = 0;
    // A knob being TURNED rather than teleported.  `sim knob <n> over <ms>` ramps the count
    // across sim time the way a finger does, and that matters now that the ui paces a setting
    // to what the hands can draw (§6.6d): a lump of forty counts in one poll is a spin no
    // hand ever performed, and the firmware is right to refuse most of it.
    int32_t turn_from = 0, turn_to = 0;
    uint64_t turn_t0 = 0;
    uint64_t turn_us = 0;  // 0 = nothing in flight
    uint64_t sw_until_us = 0;
    // ENC_SW is an INTERRUPT on IO17 (§3.3): the board cannot miss a closure, however brief.
    // Here the same edge is found by polling, and a press shorter than the poll period would
    // simply not exist -- which is a fake that behaves WORSE than the hardware it stands in
    // for.  It matters because the ux app sends `sim press down` and `up` on the real mouse
    // edges, and a quick click is easily under one 20 ms `ui` tick.  So a closure nobody has
    // read yet is held over for exactly one more read: seen once down, once up, every time.
    bool sw_seen = false;       // has a reader observed the current closure?
    bool sw_held_over = false;  // released before anybody looked -- owe them one `down`
    // movement
    AxisSt ax[2]{AxisSt{.offset_deg = kHourStartDeg}, AxisSt{.offset_deg = kMinuteStartDeg}};
    bool motor_on = false;
    bool motor_jam = false;  // sim::set_motor_jam
    bool motor_inhibit = board::motor_inhibited_default();
    // imu
    float yaw = 0.0f, pitch = 0.0f, roll = 0.0f;
    uint16_t taps = 0;
    // expander -- ELECTRICAL levels, which is what the MCP23017 driver will read.  The
    // inputs are open-drain with the expander's pull-up, so idle is HIGH and asserted is
    // LOW; `radio_off` in the CLI and the UI is the logical sense of RadioOff, inverted here.
    bool exp[expander::kSigCount] = {
        false,  // SpkSd      out  amp in shutdown at boot
        false,  // StepStby   out  both TB6612 off at boot
        false,  // Boost12En  out  12 V gate closed
        true,   // RadioOff   in   toggle open = radios enabled (a broken harness fails safe)
        true,   // PdPg       in   derived from `plugged`
        true,   // Chrg       in   derived; OD, low WHILE charging
        true,   // Fault      in   OD, idle high
        true,   // AlsInt     in   OD, idle high
        false,  // FullchgEn  out
        false,  // VbatDivEn  out
        true,   // SpkFault   in   OD, idle high
        false,  // CellTest   out
    };
    // power
    bool plugged = true;
    // Is there a cell in the holder?  The whole point of the CELL_TEST discriminator is that a
    // plugged board cannot tell from the voltage alone -- `Q2` back-feeds the holder from the
    // BAT node -- so the fake has to model the holder rather than just a number.
    bool cell_in = true;
    // How many times the Vbat divider leg has been switched in.  A fake's observation, like
    // `refreshed`: it is how a test sees that a read went through `VBAT_DIV_EN` at all rather
    // than helping itself to the node.
    uint32_t vbat_div_reads = 0;
    // outputs
    pixels::Rgbw px[pixels::kCount]{};
    bool refreshed = false;
    uint8_t warm_pct = 0;
    uint8_t cool_pct = 0;
    // audio.  `spk_active` is the fake's own idea of "the amp is up and unmuted"; the amp's
    // REGISTERS live in the 0x6C model behind the fake bus, because the driver that writes
    // them is the one the ESP32 runs (§11.2).
    bool spk_active = false;
    uint8_t vol_pct = audio::kDefaultVolPct;
    bool tone_on = false;
    uint32_t tone_hz = 0;
    uint64_t tone_off_us = 0;  // sim time; 0 = until stop()
    uint32_t tone_frames = 0;  // what the generator has actually produced
};

std::mutex g_mx;
State g_st;

uint64_t real_us() noexcept {
    using namespace std::chrono;
    static const auto t0 = steady_clock::now();
    return static_cast<uint64_t>(duration_cast<microseconds>(steady_clock::now() - t0).count());
}

// Caller holds g_mx.
uint64_t sim_us_locked() noexcept {
    const uint64_t now = real_us();
    const uint64_t d = now - g_st.real_base_us;
    return g_st.sim_base_us + static_cast<uint64_t>(static_cast<double>(d) * g_st.warp);
}

void rebase_locked() noexcept {
    g_st.sim_base_us = sim_us_locked();
    g_st.real_base_us = real_us();
}

// xorshift32 -- deterministic, so a seeded test stream is reproducible.
int32_t noise_locked() noexcept {
    if (g_st.noise_mv == 0) return 0;
    uint32_t x = g_st.rng;
    x ^= x << 13;
    x ^= x >> 17;
    x ^= x << 5;
    g_st.rng = x;
    const int32_t span = static_cast<int32_t>(g_st.noise_mv) * 2 + 1;
    return static_cast<int32_t>(x % static_cast<uint32_t>(span)) - g_st.noise_mv;
}

uint16_t clamp_mv(int32_t v) noexcept { return static_cast<uint16_t>(std::clamp(v, 0, 3300)); }

// ---- mechanism helpers (caller holds g_mx) ---------------------------------------------

int hand_idx(motor::Hand h) noexcept { return h == motor::Hand::Hour ? 0 : 1; }

float wrap360(double d) noexcept {
    d = std::fmod(d, 360.0);
    if (d < 0.0) d += 360.0;
    return static_cast<float>(d);
}

// ---- how the cube is sitting ------------------------------------------------------------
// The fake keeps ANGLES, because that is what a person setting up a scene wants to type and
// what the ux app's slider drags; the firmware reads GRAVITY, because that is the only thing
// a BNO085 can actually tell it.  This is the conversion, and it is the whole model:
//
//   yaw    the cube turned about the dial's own axis -- the plate the ux app draws, positive
//          clockwise as you look at it.  Every 30 degrees of it is one tick of §6.1d.
//   pitch  tipped away from vertical: 0 stands upright facing you, +90 lies on its back with
//          the dial to the ceiling.  At which point NOTHING in the dial plane points up, and
//          the dead zone is what the firmware is supposed to do about that.
//   roll   unused.  A third angle here would be a second way to say the first two.
//
// Output is in DIAL axes (hal.hpp): +X right across the face, +Y at the printed 12, +Z out
// through the glass.  Upright and unturned, gravity is straight down the face: (0, -g, 0).
void gravity_locked(float& gx, float& gy, float& gz) noexcept {
    constexpr double kG = 9.80665;
    constexpr double kRad = 3.14159265358979 / 180.0;
    const double y = g_st.yaw * kRad, p = g_st.pitch * kRad;
    gx = static_cast<float>(kG * std::cos(p) * std::sin(y));
    gy = static_cast<float>(-kG * std::cos(p) * std::cos(y));
    gz = static_cast<float>(-kG * std::sin(p));
}

double axis_pos_locked(int i) noexcept {
    const AxisSt& a = g_st.ax[i];
    if (a.vel == 0) return a.pos;
    const uint64_t now = sim_us_locked();
    const double dt_s = static_cast<double>(now - a.t0_us) / 1e6;
    const double p = a.pos + static_cast<double>(a.vel) * dt_s;
    return a.vel > 0 ? std::min(p, a.stop_at) : std::max(p, a.stop_at);
}

bool axis_moving_locked(int i) noexcept {
    const AxisSt& a = g_st.ax[i];
    if (a.vel == 0) return false;
    const double p = axis_pos_locked(i);
    return a.vel > 0 ? p < a.stop_at : p > a.stop_at;
}

// Freeze an axis where it currently is.  Every state change re-bases through here, which is
// what keeps the fractional position honest.
void axis_park_locked(int i) noexcept {
    g_st.ax[i].pos = axis_pos_locked(i);
    g_st.ax[i].vel = 0;
    g_st.ax[i].t0_us = sim_us_locked();
}

// What you see through the glass.  0 deg = 12 o'clock, clockwise positive.
float hand_deg_locked(int i) noexcept {
    return wrap360(axis_pos_locked(i) * 360.0 / motor::kUstepsPerRev + g_st.ax[i].offset_deg);
}

// Either hand's index mark over the window at 0 deg lights the QRE1113.  Note there is no
// interval search here: two ADC reads far enough apart WILL step over the window and miss
// it.  That aliasing is real (the phototransistor is continuous, the ADC is not) and it is
// the fastest way to find out that a homing sweep is running too fast.
float opto_from_hands_locked() noexcept {
    float best = 0.0f;
    for (int i = 0; i < 2; ++i) {
        float d = hand_deg_locked(i);
        if (d > 180.0f) d = 360.0f - d;
        float v = 0.0f;
        if (d <= kIndexHalfDeg) {
            v = 1.0f;
        } else if (d < kIndexHalfDeg + kIndexEdgeDeg) {
            v = 1.0f - (d - kIndexHalfDeg) / kIndexEdgeDeg;
        }
        best = std::max(best, v);
    }
    return kOptoDarkNorm + (1.0f - kOptoDarkNorm) * best;
}

float opto_norm_locked() noexcept { return g_st.opto_auto ? opto_from_hands_locked() : g_st.opto; }

// Charger state, behind BOTH views of the CHRG pin.  An empty holder never charges -- the
// LT3652 has nothing to push current into and deasserts -- and that is not a detail: it is
// half of what makes the CELL_TEST discriminator necessary.
bool charging_locked() noexcept {
    return g_st.plugged && g_st.cell_in && g_st.vbat_mv < kVbatFullMv;
}

// What the VBAT_SENSE node is actually at, as b_charger.py describes it.  Two FETs decide, and
// modelling them is what gives cell_test() something to find -- a fake that handed out
// `vbat_mv` regardless would pass a discriminator that cannot work on hardware.
//
//   Q2 conducting (CELL_TEST low):  holder+ is tied to the BAT node.  Plugged, that is the
//     charger -- which follows the cell while it is charging and sits at the 4.05 V float once
//     it is not, EMPTY HOLDER INCLUDED.  That last part is the problem the discriminator exists
//     for: with no cell at all the tap still reads "full".
//   Q2 off (CELL_TEST high):        the holder alone -- the cell if one is in it, else one body
//     diode below the BAT node.
uint16_t vbat_node_mv_locked() noexcept {
    const uint16_t bat =
        g_st.plugged ? (charging_locked() ? g_st.vbat_mv : kVbatFullMv) : g_st.vbat_mv;
    if (!g_st.exp[static_cast<std::size_t>(expander::Sig::CellTest)]) return bat;
    if (g_st.cell_in) return g_st.vbat_mv;
    return static_cast<uint16_t>(bat > kQ2DiodeMv ? bat - kQ2DiodeMv : 0);
}

// One truth about every expander pin, read by BOTH views of it: the named-signal surface
// (hal::expander, what the firmware uses today) and the register surface (hal::i2c, what a
// real Mcp23017 driver will use).  Two independent fakes that could disagree would be a
// simulator that fails a driver the hardware would have passed.
bool sig_level_locked(expander::Sig s) noexcept {
    switch (s) {
        // Derived rather than stored, so there is exactly one truth about being plugged in
        // and one about charging -- power::read() and this pin cannot disagree.
        // ACTIVE-LOW, like every other open-drain input on this chip: the CH224K pulls PG
        // down when the 15 V contract is up (power_values.md, and §12.0.11 step 6 expects
        // `PD_PG 0` with the brick in).  The fake had it the other way round until 2026-09-13,
        // which would have had the target and clocksim print opposite bits for the same board.
        case expander::Sig::PdPg:
            return !g_st.plugged;
        case expander::Sig::Chrg:
            return !charging_locked();  // OD: low while charging
        case expander::Sig::StepStby:
            return g_st.motor_on;
        default:
            return g_st.exp[static_cast<std::size_t>(s)];
    }
}

// The knob count as it stands right now, mid-ramp included.  Evaluated lazily like the axes:
// no thread, exact under `sim warp`, and a ramp that has run out settles into `count`.
int32_t knob_count_locked() noexcept {
    if (g_st.turn_us == 0) return g_st.count;
    const uint64_t dt = sim_us_locked() - g_st.turn_t0;
    if (dt >= g_st.turn_us) {
        g_st.count = g_st.turn_to;
        g_st.turn_us = 0;
        return g_st.count;
    }
    const int64_t span = static_cast<int64_t>(g_st.turn_to) - g_st.turn_from;
    return g_st.turn_from + static_cast<int32_t>(span * static_cast<int64_t>(dt) /
                                                 static_cast<int64_t>(g_st.turn_us));
}

// Freeze the ramp where it is, so the next turn accumulates onto what the user has already
// been given rather than onto where the last one was heading.
void knob_settle_locked() noexcept {
    g_st.count = knob_count_locked();
    g_st.turn_us = 0;
}

// ---- persistent settings ----------------------------------------------------------------
// `key = value` lines, read whole and written whole.  There are a handful of keys and a
// laptop's page cache in front of the file, so anything cleverer would be cleverness for its
// own sake.  The path is set by the app (clocksim), never defaulted here: a test binary that
// wrote calibration into somebody's home directory would be a fake with side effects, and the
// honest answer for "no store configured" is the same NotPresent as an unfitted device.
// A value is an int32 or, since the alarm tone, a quoted string: `sto.tone = "birds.wav"`.
struct Kv {
    std::string key;
    int32_t val = 0;
    std::string str;
    bool is_str = false;
};
std::string g_store_path;
std::vector<Kv> g_store;

void store_load_locked() noexcept {
    g_store.clear();
    if (g_store_path.empty()) return;
    std::FILE* f = std::fopen(g_store_path.c_str(), "r");
    if (!f) return;  // never written yet -- every key is simply absent
    char line[256];
    while (std::fgets(line, sizeof line, f)) {
        char* eq = std::strchr(line, '=');
        if (!eq) continue;
        *eq = '\0';
        std::string k{line};
        while (!k.empty() && (k.back() == ' ' || k.back() == '\t')) k.pop_back();
        if (k.empty()) continue;
        const char* v = eq + 1;
        while (*v == ' ' || *v == '\t') ++v;
        if (*v == '"') {
            std::string str{v + 1};
            const auto close = str.rfind('"');
            str = close == std::string::npos ? std::string{} : str.substr(0, close);
            g_store.push_back({k, 0, str, true});
        } else {
            g_store.push_back({k, static_cast<int32_t>(std::strtol(v, nullptr, 10)), {}, false});
        }
    }
    std::fclose(f);
}

bool store_save_locked() noexcept {
    if (g_store_path.empty()) return false;
    std::FILE* f = std::fopen(g_store_path.c_str(), "w");
    if (!f) return false;
    for (auto const& kv : g_store) {
        if (kv.is_str) {
            std::fprintf(f, "%s = \"%s\"\n", kv.key.c_str(), kv.str.c_str());
        } else {
            std::fprintf(f, "%s = %d\n", kv.key.c_str(), kv.val);
        }
    }
    std::fclose(f);
    return true;
}

}  // namespace

// ============================ hal::clock_ ================================================
namespace clock_ {

uint64_t micros() noexcept {
    std::lock_guard lk{g_mx};
    return sim_us_locked();
}

uint32_t millis() noexcept { return static_cast<uint32_t>(micros() / 1000); }

// Real time on purpose: this paces the console and the stream producer, and warping it
// would make `sensor ... stream 100` sample at 6 kHz when warp is 60.
void sleep_ms(uint32_t ms) noexcept { std::this_thread::sleep_for(std::chrono::milliseconds(ms)); }

// The fake has no oscillator to fail, so it answers from the presence flag -- and `sim present
// xtal32k off` is then how you exercise the fallback path without a board that has a dud
// crystal on it (§13.9: model what the firmware branches on).
SlowSrc slow_src() noexcept {
    return board::present(board::Dev::Xtal32k) ? SlowSrc::Xtal32k : SlowSrc::RcSlow;
}

}  // namespace clock_

// ============================ hal::adc ===================================================
namespace adc {

Result<uint16_t> read_mv(Ch ch) noexcept {
    std::lock_guard lk{g_mx};
    switch (ch) {
        case Ch::Opto: {
            if (!board::present(board::Dev::Opto)) return Result<uint16_t>::bad(Status::NotPresent);
            // Inverted, like the real sensor: norm 1 (on the mark) is the LOW end.
            const float span = static_cast<float>(kOptoClearMv - kOptoMarkMv);
            const int32_t mv =
                static_cast<int32_t>(kOptoClearMv - opto_norm_locked() * span) + noise_locked();
            return Result<uint16_t>::good(clamp_mv(mv));
        }
        case Ch::Vbat: {
            if (!board::present(board::Dev::Vbat)) return Result<uint16_t>::bad(Status::NotPresent);
            // The divider's bottom leg is `Q3`, and it is OPEN by default -- 100k/100k across a
            // backup cell is a permanent 20 uA drain otherwise (power.md).  So switch it in,
            // read, and put it back the way it was found, exactly as hal_esp.cpp does; the
            // caller above never learns that either of us has a FET.  (No settling wait here:
            // C110's 25 ms is real hardware, and burning it under `sim warp` would slow every
            // test that samples the cell.)
            const auto leg = static_cast<std::size_t>(expander::Sig::VbatDivEn);
            const bool was = g_st.exp[leg];
            g_st.exp[leg] = true;
            ++g_st.vbat_div_reads;
            const int32_t mv = vbat_node_mv_locked() + noise_locked();
            g_st.exp[leg] = was;
            return Result<uint16_t>::good(static_cast<uint16_t>(std::clamp<int32_t>(mv, 0, 5000)));
        }
    }
    return Result<uint16_t>::bad(Status::BadArg);
}

Result<float> read_opto_norm() noexcept {
    const auto mv = read_mv(Ch::Opto);
    if (!mv.ok()) return Result<float>::bad(mv.st);
    return Result<float>::good(adc::opto_norm_from_mv(mv.v));
}

}  // namespace adc

// ============================ hal::knob ==================================================
namespace knob {

Result<State> read() noexcept {
    std::lock_guard lk{g_mx};
    if (!board::present(board::Dev::Knob)) return Result<State>::bad(Status::NotPresent);
    State s{};
    s.count = knob_count_locked();
    s.delta = s.count - g_st.last_read;
    bool down = sim_us_locked() < g_st.sw_until_us;
    if (!down && g_st.sw_held_over) {
        down = true;                // the closure this reader would otherwise have missed
        g_st.sw_held_over = false;  // and the next read sees it open again
    }
    if (down) g_st.sw_seen = true;
    s.sw = down;
    // The fake has no pin, so the closure itself is the raw level -- the held-over press is
    // the part that is synthetic, and it is exactly what `sw` adds on top.
    s.sw_raw = sim_us_locked() < g_st.sw_until_us;
    // The fake has no pads.  Rather than invent a quadrature waveform nothing reads, derive a
    // plausible A/B from the count so the field is never stale -- 4 counts per quadrature
    // cycle, which is what x4 decoding means.
    // Gray code, which is what quadrature IS: over four counts the pair walks 00, 10, 11, 01
    // and never changes both lines at once.  Getting that wrong here would teach a bench the
    // wrong pattern to look for on the real pads.
    s.a_raw = (((s.count + 1) >> 1) & 1) != 0;
    s.b_raw = ((s.count >> 1) & 1) != 0;
    g_st.last_read = s.count;
    return Result<State>::good(s);
}

}  // namespace knob

// ============================ hal::motor =================================================
namespace motor {

Status enable(bool on) noexcept {
    std::lock_guard lk{g_mx};
    if (!board::present(board::Dev::Motor)) return Status::NotPresent;
    // Same rule as the target: refused on the way up only (hal.hpp).
    if (on && g_st.motor_inhibit) return Status::Denied;
    if (on == g_st.motor_on) return Status::Ok;
    // Dropping STEP_STBY kills the coils, and dead coils do not turn a rotor.  Parking both
    // axes here is what makes `motion` do the MotorPower handshake (§6.1) honestly instead
    // of discovering on the bench that the hands never moved.
    if (!on) {
        axis_park_locked(0);
        axis_park_locked(1);
    }
    g_st.motor_on = on;
    g_st.exp[static_cast<std::size_t>(expander::Sig::StepStby)] = on;
    return Status::Ok;
}

bool enabled() noexcept {
    std::lock_guard lk{g_mx};
    return g_st.motor_on;
}

Status run(Hand h, int32_t usteps_per_s, int32_t stop_at) noexcept {
    std::lock_guard lk{g_mx};
    if (!board::present(board::Dev::Motor)) return Status::NotPresent;
    if (!g_st.motor_on) return Status::NotReady;  // STEP_STBY is low: the coils are dead
    const int i = hand_idx(h);
    axis_park_locked(i);
    if (g_st.motor_jam) return Status::Ok;  // accepted, and nothing turns
    // A velocity pointing away from the target is a caller bug, not a slow move: reject it
    // rather than run the hand into the next revolution.
    const double delta = static_cast<double>(stop_at) - g_st.ax[i].pos;
    if (usteps_per_s == 0 || (delta > 0) != (usteps_per_s > 0)) {
        if (delta != 0.0 && usteps_per_s != 0) return Status::BadArg;
        return Status::Ok;  // already there, or asked to stand still
    }
    g_st.ax[i].vel = usteps_per_s;
    g_st.ax[i].stop_at = stop_at;
    return Status::Ok;
}

Status hold(Hand h) noexcept {
    std::lock_guard lk{g_mx};
    if (!board::present(board::Dev::Motor)) return Status::NotPresent;
    axis_park_locked(hand_idx(h));
    return Status::Ok;
}

Status adopt(Hand h, int32_t pos) noexcept {
    std::lock_guard lk{g_mx};
    if (!board::present(board::Dev::Motor)) return Status::NotPresent;
    const int i = hand_idx(h);
    axis_park_locked(i);
    // Renaming the coordinate must not teleport the hand: the offset absorbs the change.
    // This is the one place the fake's mechanism and the firmware's bookkeeping meet.
    const double moved = g_st.ax[i].pos - static_cast<double>(pos);
    g_st.ax[i].offset_deg = wrap360(g_st.ax[i].offset_deg + moved * 360.0 / kUstepsPerRev);
    g_st.ax[i].pos = pos;
    g_st.ax[i].stop_at = pos;
    return Status::Ok;
}

Status inhibit(bool on) noexcept {
    std::lock_guard lk{g_mx};
    g_st.motor_inhibit = on;
    if (on && g_st.motor_on) {
        axis_park_locked(0);
        axis_park_locked(1);
        g_st.motor_on = false;
        g_st.exp[static_cast<std::size_t>(expander::Sig::StepStby)] = false;
    }
    return Status::Ok;
}

bool inhibited() noexcept {
    std::lock_guard lk{g_mx};
    return g_st.motor_inhibit;
}

// Bench-only on the target; the fake has no coils, so it only keeps the contract.
namespace {
Decay g_decay = Decay::Slow;
}
void set_decay(Decay d) noexcept { g_decay = d; }
Decay decay() noexcept { return g_decay; }

Status coils(Hand h, int16_t a_pm, int16_t b_pm) noexcept {
    std::lock_guard lk{g_mx};
    if (!board::present(board::Dev::Motor)) return Status::NotPresent;
    if (!g_st.motor_on) return Status::NotReady;
    if (a_pm < -1000 || a_pm > 1000 || b_pm < -1000 || b_pm > 1000) return Status::BadArg;
    axis_park_locked(hand_idx(h));
    return Status::Ok;
}

Axis state(Hand h) noexcept {
    std::lock_guard lk{g_mx};
    const int i = hand_idx(h);
    Axis a{};
    a.pos = static_cast<int32_t>(std::llround(axis_pos_locked(i)));
    a.moving = axis_moving_locked(i);
    a.vel = a.moving ? g_st.ax[i].vel : 0;
    return a;
}

}  // namespace motor

// ============================ hal::pixels ================================================
namespace pixels {

Status set(std::size_t i, Rgbw c) noexcept {
    if (i >= kCount) return Status::BadArg;
    std::lock_guard lk{g_mx};
    if (!board::present(board::Dev::Pixels)) return Status::NotPresent;
    g_st.px[i] = c;
    g_st.refreshed = false;
    return Status::Ok;
}

Status set_all(Rgbw c) noexcept {
    std::lock_guard lk{g_mx};
    if (!board::present(board::Dev::Pixels)) return Status::NotPresent;
    for (auto& p : g_st.px) p = c;
    g_st.refreshed = false;
    return Status::Ok;
}

Status refresh() noexcept {
    std::lock_guard lk{g_mx};
    if (!board::present(board::Dev::Pixels)) return Status::NotPresent;
    g_st.refreshed = true;
    return Status::Ok;
}

Rgbw get(std::size_t i) noexcept {
    std::lock_guard lk{g_mx};
    return i < kCount ? g_st.px[i] : Rgbw{};
}

}  // namespace pixels

// ============================ hal::wake ==================================================
namespace wake {

Status set(uint8_t warm_pct, uint8_t cool_pct) noexcept {
    if (warm_pct > 100 || cool_pct > 100) return Status::BadArg;
    std::lock_guard lk{g_mx};
    if (!board::present(board::Dev::WakeLed)) return Status::NotPresent;
    // §6.8 interlock 4: the 12 V boost is plugged-only, so the wake light must be gated
    // off on battery.  The fake enforces it, so a service that forgets fails here first.
    if (!g_st.plugged && (warm_pct || cool_pct)) return Status::Denied;
    g_st.warm_pct = warm_pct;
    g_st.cool_pct = cool_pct;
    return Status::Ok;
}

uint8_t warm() noexcept {
    std::lock_guard lk{g_mx};
    return g_st.warm_pct;
}
uint8_t cool() noexcept {
    std::lock_guard lk{g_mx};
    return g_st.cool_pct;
}

}  // namespace wake

// ============================ hal::i2c ===================================================
// The bus is a table of slaves, and a slave is either MODELLED or merely present.  The
// distinction is §13.9 item 9's, made once here: a modelled device has a register file that
// the shipping driver drives, so `hal::als::read()` on this host runs tsl2591.cpp.  A merely
// present device ACKs its address so a scan finds it and answers nothing else, which is all
// the firmware branches on for it today.
namespace i2c {
namespace {

// Forward-declared so the table can point at it: the MCP23017's model needs g_st, so unlike
// the daughterboard models it cannot live in a file of its own.
Status mcp_xfer(const uint8_t* w, std::size_t wn, uint8_t* r, std::size_t rn) noexcept;
void mcp_reset_locked() noexcept;

struct Slave {
    uint8_t addr;
    board::Dev dev;
    host::model::Xfer xfer;    // nullptr: ACKs its address, reads back zeros
    void (*reset)() noexcept;  // nullptr: nothing to put back
};

constexpr Slave kBus[] = {
    {0x20, board::Dev::Expander, &mcp_xfer, &mcp_reset_locked},
    {0x29, board::Dev::Als, &host::model::tsl2591, &host::model::tsl2591_reset},
    // 0x4A BNO085: no model, deliberately (§13.9 item 9).  An SHTP responder is a week of
    // work to test code only real silicon can invalidate, so `hal::imu` here stays the
    // angle-based fake and bno085.cpp is exercised on target.
    {0x4A, board::Dev::Imu, nullptr, nullptr},
    {0x6C, board::Dev::Amp, &host::model::tas5760m, &host::model::tas5760m_reset},
    {0x77, board::Dev::Env, &host::model::bme688, &host::model::bme688_reset},
};

const Slave* find(uint8_t addr) noexcept {
    for (auto const& s : kBus) {
        if (s.addr == addr) return &s;
    }
    return nullptr;
}

}  // namespace

Result<std::size_t> scan(uint8_t* out, std::size_t cap) noexcept {
    std::lock_guard lk{g_mx};
    std::size_t n = 0;
    for (auto const& s : kBus) {
        if (!board::present(s.dev)) continue;
        if (n < cap) out[n] = s.addr;
        ++n;
    }
    return Result<std::size_t>::good(n);
}

// ---- the MCP23017 at 0x20, at register level (§11.2, §13.9 item 9) ----------------------
// The expander is the one device on the MAIN board a driver is written against, and a
// driver is exactly what a register file catches: BANK ordering, IODIR polarity, GPPU on
// GPB3 (R-BOARD-4), the OLAT/GPIO distinction.  Modelled: the registers the firmware
// branches on.  Not modelled: interrupt-on-change, IOCON.BANK = 1.
namespace {

enum Reg : uint8_t {
    IODIRA = 0x00,
    IODIRB = 0x01,
    GPPUA = 0x0C,
    GPPUB = 0x0D,
    GPIOA = 0x12,
    GPIOB = 0x13,
    OLATA = 0x14,
    OLATB = 0x15,
    kRegCount = 0x16,
};

// Sig order IS the pin order (hal.hpp): 0-3 are GPA0-3, 4-11 are GPB0-7.  The static_assert
// is the guard -- reorder the enum and this stops compiling rather than silently swapping
// SPK_SD for CELL_TEST on a bench where both are one bit in a hex byte.
constexpr std::size_t kPortASigs = 4;
static_assert(static_cast<std::size_t>(expander::Sig::RadioOff) == 3);
static_assert(static_cast<std::size_t>(expander::Sig::PdPg) == kPortASigs);
static_assert(expander::kSigCount == kPortASigs + 8);

uint8_t g_mcp[kRegCount] = {0xFF, 0xFF};  // POR: both IODIR all-inputs, everything else 0

// The live pin levels as one byte per port, so a GPIO read answers what the pins are doing
// and not what was last written to them.
uint8_t port_level_locked(bool port_b) noexcept {
    uint8_t v = 0;
    const std::size_t first = port_b ? kPortASigs : 0;
    const std::size_t n = port_b ? 8 : kPortASigs;
    for (std::size_t i = 0; i < n; ++i) {
        if (sig_level_locked(static_cast<expander::Sig>(first + i)))
            v |= static_cast<uint8_t>(1u << i);
    }
    return v;
}

// A write reaches a pin only where IODIR says the pin is an output -- which is what makes
// "the driver forgot to clear IODIR" a visible failure here instead of on the bench.
void port_drive_locked(bool port_b, uint8_t val) noexcept {
    const uint8_t dir = g_mcp[port_b ? IODIRB : IODIRA];
    const std::size_t first = port_b ? kPortASigs : 0;
    const std::size_t n = port_b ? 8 : kPortASigs;
    for (std::size_t i = 0; i < n; ++i) {
        const auto s = static_cast<expander::Sig>(first + i);
        if ((dir & (1u << i)) || !expander::is_output(s)) continue;  // input: not ours to drive
        g_st.exp[static_cast<std::size_t>(s)] = (val & (1u << i)) != 0;
    }
}

uint8_t mcp_read_locked(uint8_t reg) noexcept {
    if (reg == GPIOA || reg == GPIOB) return port_level_locked(reg == GPIOB);
    return g_mcp[reg];
}

void mcp_write_locked(uint8_t reg, uint8_t val) noexcept {
    g_mcp[reg] = val;
    // GPIO and OLAT are the same latch seen twice; writing either drives the outputs.
    if (reg == GPIOA || reg == OLATA) {
        g_mcp[GPIOA] = g_mcp[OLATA] = val;
        port_drive_locked(false, val);
    } else if (reg == GPIOB || reg == OLATB) {
        g_mcp[GPIOB] = g_mcp[OLATB] = val;
        port_drive_locked(true, val);
    }
}

// BANK = 0, SEQOP = 0: the address pointer advances after every byte and wraps at 0x15.
// Modelled because a burst read of both GPIO ports in one transaction is the obvious next
// thing the driver will do, and a model that only answered single bytes would fail it.
Status mcp_xfer(const uint8_t* w, std::size_t wn, uint8_t* r, std::size_t rn) noexcept {
    if (wn == 0) return Status::BadArg;  // the chip always wants an address first
    uint8_t reg = w[0];
    if (reg >= kRegCount) return Status::BadArg;
    for (std::size_t i = 1; i < wn; ++i) {
        mcp_write_locked(reg, w[i]);
        reg = static_cast<uint8_t>((reg + 1) % kRegCount);
    }
    for (std::size_t i = 0; i < rn; ++i) {
        r[i] = mcp_read_locked(reg);
        reg = static_cast<uint8_t>((reg + 1) % kRegCount);
    }
    return Status::Ok;
}

// Called by sim::reset(): the register file is device state, and a test that inherits the
// previous test's IODIR is a test that passes for the wrong reason.
void mcp_reset_locked() noexcept {
    for (auto& r : g_mcp) r = 0;
    g_mcp[IODIRA] = g_mcp[IODIRB] = 0xFF;
}

// Every model back to power-on, in one place, so `sim reset` cannot forget one.
void models_reset_locked() noexcept {
    for (auto const& s : kBus) {
        if (s.reset) s.reset();
    }
}

}  // namespace

Status write_read(uint8_t addr, const uint8_t* w, std::size_t wn, uint8_t* r,
                  std::size_t rn) noexcept {
    if ((wn && !w) || (rn && !r)) return Status::BadArg;
    if (!wn && !rn) return Status::BadArg;
    std::lock_guard lk{g_mx};
    const Slave* s = find(addr);
    // An address nobody lives at and an unplugged daughterboard are the same answer, and
    // that is right: NotPresent is D16's "the hardware is absent", not an error.
    if (!s || !board::present(s->dev)) return Status::NotPresent;
    if (s->xfer) return s->xfer(w, wn, r, rn);
    for (std::size_t i = 0; i < rn; ++i) r[i] = 0;  // ACKs, says nothing
    return Status::Ok;
}

Status write(uint8_t addr, const uint8_t* buf, std::size_t n) noexcept {
    return write_read(addr, buf, n, nullptr, 0);
}

Status read(uint8_t addr, uint8_t* buf, std::size_t n) noexcept {
    return write_read(addr, nullptr, 0, buf, n);
}

Result<uint8_t> read_reg(uint8_t addr, uint8_t reg) noexcept {
    uint8_t v = 0;
    const Status st = write_read(addr, &reg, 1, &v, 1);
    return st == Status::Ok ? Result<uint8_t>::good(v) : Result<uint8_t>::bad(st);
}

Status read_regs(uint8_t addr, uint8_t reg, uint8_t* out, std::size_t n) noexcept {
    return write_read(addr, &reg, 1, out, n);
}

Status write_reg(uint8_t addr, uint8_t reg, uint8_t val) noexcept {
    const uint8_t buf[2] = {reg, val};
    return write(addr, buf, sizeof buf);
}

}  // namespace i2c

// ============================ hal::imu ===================================================
namespace imu {

Result<State> read() noexcept {
    std::lock_guard lk{g_mx};
    if (!board::present(board::Dev::Imu)) return Result<State>::bad(Status::NotPresent);
    State s{};
    s.yaw_deg = g_st.yaw;
    s.pitch_deg = g_st.pitch;
    s.roll_deg = g_st.roll;
    gravity_locked(s.gx, s.gy, s.gz);
    s.taps = g_st.taps;  // monotonic: the caller diffs, so a missed poll costs no taps
    return Result<State>::good(s);
}

// There is no SHTP link here to be alive or wedged (§13.9 item 9), so the honest answer is
// the presence flag: `sim present imu off` is how R-BOARD-3's degraded path gets exercised.
Link link() noexcept {
    std::lock_guard lk{g_mx};
    const bool up = board::present(board::Dev::Imu);
    return Link{up ? 1u : 0u, 0u, up ? 0u : kNever, up};
}

}  // namespace imu

// ============================ hal::als / hal::env ========================================
// The shipping drivers, running against the register models behind the fake bus.  Not a
// forwarding stub each -- these two lines ARE §11.2: the same tsl2591.cpp and bme688.cpp the
// ESP32 links, exercised by `test_host` with no hardware anywhere in the room.
namespace als {
Result<State> read() noexcept { return tsl2591::read(); }
}  // namespace als

namespace env {
Result<State> read() noexcept { return bme688::read(); }
}  // namespace env

// ============================ hal::expander ==============================================
namespace expander {

Result<bool> get(Sig s) noexcept {
    std::lock_guard lk{g_mx};
    if (static_cast<std::size_t>(s) >= kSigCount) return Result<bool>::bad(Status::BadArg);
    if (!board::present(board::Dev::Expander)) return Result<bool>::bad(Status::NotPresent);
    return Result<bool>::good(sig_level_locked(s));
}

Status set(Sig s, bool level) noexcept {
    if (static_cast<std::size_t>(s) >= kSigCount) return Status::BadArg;
    // An input is the outside world's to drive.  Saying so is more useful than silently
    // accepting a write that the hardware would ignore.
    if (!is_output(s)) return Status::BadArg;
    std::lock_guard lk{g_mx};
    if (!board::present(board::Dev::Expander)) return Status::NotPresent;
    // §6.8 interlock 1: BOOST12_EN is never asserted unless PD_PG reads high.  The fake
    // enforces it for the same reason it enforces the wake-light gate -- a service that
    // forgets fails here, not on a bench with a 12 V rail up on battery.
    if (s == Sig::Boost12En && level && !g_st.plugged) return Status::Denied;
    g_st.exp[static_cast<std::size_t>(s)] = level;
    if (s == Sig::StepStby) g_st.motor_on = level;
    return Status::Ok;
}

}  // namespace expander

// ============================ hal::audio =================================================
// There is no sound here and there is not going to be one.  What this side DOES do is run the
// same two pieces of shipping code the ESP32 runs -- the TAS5760M driver against the 0x6C
// register model, and the sine generator -- so that the register set, the start-up ORDER and
// the envelope are all covered before the board is on the bench (§11.2).
//
// The one thing it fakes outright is time: there is no DMA to feed, so the tone ends when sim
// time says it does rather than when 48 000 frames have been consumed.  `sim warp` therefore
// works on a beep exactly as it does on a sunrise.
//
// LOCKING, and it is the trap this file sets for you: hal::i2c takes `g_mx` itself, and it is
// a plain std::mutex.  Every tas5760m:: call below therefore happens with the lock RELEASED,
// exactly as hal::als and hal::env already do -- holding it across a driver call deadlocks on
// the first register write.
namespace audio {
namespace {

// The datasheet's order, the same one audio_esp.cpp walks: clocks (which here is nothing),
// configure muted, SPK_SD high, unmute.  Running it through tas5760m.cpp rather than setting a
// bool is what makes a reordered ESP-side sequence a host failure.
// The host's start is synchronous, so its failure latch is trivially in step -- but it exists
// and is reported through the same State fields, so a test can assert on the CLI's wait-for-
// the-answer path rather than on a duration.
Status g_start_st = Status::Ok;
const char* g_start_step = nullptr;
uint32_t g_start_seq = 0;

// The stream.  Same Ring and Mixer as the target (pcm.hpp), drained lazily in SIM time: every
// call that reports on the audio first pulls through the mixer the frames the DMA would have
// taken since the last one.  So the fake underruns when `storage` falls behind, primes, ramps
// and ends exactly where the board would -- the samples go nowhere, the counters are real.
// All under g_mx.
pcm::Ring g_ring;
std::vector<int16_t> g_ring_buf;
pcm::Mixer g_mix;
bool g_stream = false;  // the stream is the live source
bool g_eof = false;
uint64_t g_drain_us = 0;  // sim time the ring was last drained up to
uint32_t g_stream_seq = 0;

// Caller holds g_mx.  True when the stream just finished and the amp should be parked.
bool drain_locked() noexcept {
    if (!g_stream) return false;
    const uint64_t now = sim_us_locked();
    if (now <= g_drain_us) return false;
    uint64_t due = (now - g_drain_us) * kRateHz / 1'000'000ull;
    g_drain_us += due * 1'000'000ull / kRateHz;
    int16_t scratch[512 * 2];
    while (due > 0 && !g_mix.done()) {
        // Nothing the mixer could do with more time: waiting to prime, or starving.  One fill
        // registers the state (an underrun is counted once per gap) and the rest of the
        // interval is skipped -- `sim warp 1000` must not spin here for a simulated hour.
        const bool waiting =
            !g_mix.primed() && !g_eof && g_ring.level() < kRateHz * pcm::kPrimeMs / 1000u;
        const bool starving = g_mix.primed() && !g_eof && g_ring.level() == 0;
        const std::size_t n = due < 512 ? static_cast<std::size_t>(due) : 512u;
        g_mix.fill(g_ring, g_eof, scratch, n);
        due -= n;
        if (waiting || starving) break;
    }
    if (!g_mix.done()) return false;
    g_stream = false;
    g_st.tone_on = false;
    return true;
}

Status finish_start(const char* step, Status st) noexcept {
    std::lock_guard lk{g_mx};
    g_start_step = st == Status::Ok ? nullptr : step;
    g_start_st = st;
    ++g_start_seq;
    return st;
}

Status bring_up_inner() noexcept {
    {
        std::lock_guard lk{g_mx};
        if (g_st.spk_active) return Status::Ok;
        g_st.exp[static_cast<std::size_t>(expander::Sig::SpkSd)] = false;
    }
    uint8_t vol = 0;
    {
        std::lock_guard lk{g_mx};
        vol = g_st.vol_pct;
    }
    if (const Status st = tas5760m::configure(true, tas5760m::db_for_pct(vol)); st != Status::Ok)
        return st;
    {
        std::lock_guard lk{g_mx};
        g_st.exp[static_cast<std::size_t>(expander::Sig::SpkSd)] = true;
    }
    if (const Status st = tas5760m::set_mute(false); st != Status::Ok) return st;
    std::lock_guard lk{g_mx};
    g_st.spk_active = true;
    return Status::Ok;
}

Status bring_up() noexcept {
    const Status st = bring_up_inner();
    return finish_start("cfg", st);
}

void bring_down() noexcept {
    {
        std::lock_guard lk{g_mx};
        if (!g_st.spk_active) return;
    }
    (void)tas5760m::set_mute(true);
    std::lock_guard lk{g_mx};
    g_st.exp[static_cast<std::size_t>(expander::Sig::SpkSd)] = false;
    g_st.spk_active = false;
    g_st.tone_on = false;
}

// The tone's own clock.  Called at the top of everything that reports on it, because nothing
// on this side is running a writer task to notice the deadline on its own.  Returns true when
// it just expired, so the caller can park the amp outside the lock.
bool tone_expired() noexcept {
    std::lock_guard lk{g_mx};
    if (!g_st.tone_on || g_st.tone_off_us == 0) return false;
    if (sim_us_locked() < g_st.tone_off_us) return false;
    g_st.tone_on = false;
    return true;
}

void age_tone() noexcept {
    bool finished = false;
    {
        std::lock_guard lk{g_mx};
        finished = drain_locked();
    }
    if (tone_expired() || finished) bring_down();
}

}  // namespace

Status enable(bool on) noexcept {
    if (!board::present(board::Dev::Amp)) return Status::NotPresent;
    if (on) return bring_up();
    bring_down();
    return Status::Ok;
}

bool active() noexcept {
    age_tone();
    std::lock_guard lk{g_mx};
    return g_st.spk_active && !tas5760m::shadow().muted;
}

Status set_volume_pct(uint8_t pct) noexcept {
    if (pct > 100) return Status::BadArg;
    // The ceiling is R-AUDIO-1's, not the fake's, so it is enforced identically on both sides
    // -- a `ui` that walks its volume gauge past it must fail here too.
    if (pct > kMaxVolPct) return Status::Denied;
    {
        std::lock_guard lk{g_mx};
        g_st.vol_pct = pct;
    }
    // No presence check: set_volume_db() remembers the level and answers NotPresent, which is
    // what a devkit with no amp fitted should do -- D16 says absence is not an error, and a
    // setting that silently reverts when the part arrives is worse than one that waits.
    return tas5760m::set_volume_db(tas5760m::db_for_pct(pct));
}

uint8_t volume_pct() noexcept {
    std::lock_guard lk{g_mx};
    return g_st.vol_pct;
}

Status tone(uint32_t hz, uint32_t ms) noexcept {
    if (hz < hal::tone::kMinHz || hz > hal::tone::kMaxHz) return Status::BadArg;
    if (!board::present(board::Dev::Amp)) return Status::NotPresent;
    if (const Status st = bring_up(); st != Status::Ok) return st;
    // Generate one block for real.  Nothing listens to it, but it is what proves the generator
    // is reachable from this path, and it gives a test a frame count that only moves when a
    // tone actually ran.
    hal::tone::Sine gen;
    gen.start(hz, kRateHz, 1.0f, ms);
    int16_t block[64 * 2];
    const std::size_t made = gen.fill(block, 64);
    std::lock_guard lk{g_mx};
    g_stream = false;  // a tone replaces the stream
    g_st.tone_frames = static_cast<uint32_t>(made);
    g_st.tone_on = true;
    g_st.tone_hz = hz;
    g_st.tone_off_us = ms == 0 ? 0 : sim_us_locked() + static_cast<uint64_t>(ms) * 1000ull;
    return Status::Ok;
}

Status stop() noexcept {
    {
        std::lock_guard lk{g_mx};
        g_st.tone_on = false;
        g_mix.release();
        g_stream = false;
    }
    bring_down();
    return Status::Ok;
}

Status stream_open(uint32_t ramp_ms) noexcept {
    if (!board::present(board::Dev::Amp)) return Status::NotPresent;
    // Synchronous here, as tone() is: the failure latch is published before this returns.
    if (const Status st = bring_up(); st != Status::Ok) return st;
    std::lock_guard lk{g_mx};
    if (g_ring_buf.empty()) {
        g_ring_buf.resize(static_cast<std::size_t>(kRateHz) * kStreamRingMs / 1000u);
        g_ring.attach(g_ring_buf.data(), g_ring_buf.size());
    }
    g_ring.clear();
    g_mix.start(kRateHz, ramp_ms);
    g_eof = false;
    g_stream = true;
    g_drain_us = sim_us_locked();
    ++g_stream_seq;
    g_st.tone_on = true;  // "playing", as far as state() and playing() are concerned
    g_st.tone_hz = 0;
    g_st.tone_off_us = 0;
    return Status::Ok;
}

std::size_t stream_write(const int16_t* mono, std::size_t n) noexcept {
    if (!mono) return 0;
    std::lock_guard lk{g_mx};
    if (!g_stream || g_eof) return 0;
    return g_ring.write(mono, n);
}

std::size_t stream_space() noexcept {
    age_tone();
    std::lock_guard lk{g_mx};
    if (!g_stream || g_eof) return 0;
    return g_ring.space();
}

void stream_end() noexcept {
    std::lock_guard lk{g_mx};
    g_eof = true;
}

Stream stream() noexcept {
    age_tone();
    std::lock_guard lk{g_mx};
    Stream st{};
    st.open = g_stream && !g_mix.done();
    st.primed = st.open && g_mix.primed();
    st.level = static_cast<uint32_t>(g_ring_buf.empty() ? 0u : g_ring.level());
    st.cap = static_cast<uint32_t>(g_ring.capacity());
    st.underruns = g_mix.underruns();
    st.played = g_mix.frames_played();
    st.seq = g_stream_seq;
    return st;
}

bool playing() noexcept {
    age_tone();
    std::lock_guard lk{g_mx};
    return g_st.tone_on;
}

uint32_t start_seq() noexcept {
    std::lock_guard lk{g_mx};
    return g_start_seq;
}

// The pin test is TARGET-ONLY and says so.  There are no pads here, and a fake that answered
// Ok would be a fake the bench could not tell from a board -- which is the one thing D14
// forbids.  `audio clk` is different: the geometry is a decision, so it is remembered and
// reported on both sides and the CLI row stays testable.
Status pin_drive(Pin, bool) noexcept { return Status::NotPresent; }
Status pin_release() noexcept { return Status::NotPresent; }
Result<Probe> probe_pins() noexcept { return Result<Probe>::bad(Status::NotPresent); }

uint16_t g_mclk_mult = 256;
uint8_t g_slot_bits = 16;

Status set_clocking(uint16_t mclk_multiple, uint8_t slot_bits) noexcept {
    if (slot_bits != 16 && slot_bits != 32) return Status::BadArg;
    switch (mclk_multiple) {
        case 128:
        case 192:
        case 256:
        case 384:
        case 512:
            break;
        default:
            return Status::BadArg;
    }
    if (mclk_multiple % (2u * slot_bits) != 0) return Status::BadArg;
    std::lock_guard lk{g_mx};
    g_mclk_mult = mclk_multiple;
    g_slot_bits = slot_bits;
    return Status::Ok;
}

void clocking(uint16_t& mclk_multiple, uint8_t& slot_bits) noexcept {
    std::lock_guard lk{g_mx};
    mclk_multiple = g_mclk_mult;
    slot_bits = g_slot_bits;
}

Result<State> state() noexcept {
    if (!board::present(board::Dev::Amp)) return Result<State>::bad(Status::NotPresent);
    age_tone();
    const auto sh = tas5760m::shadow();
    std::lock_guard lk{g_mx};
    State s{};
    s.clocks = g_st.spk_active;  // no port to ask; the amp being up is the whole of it here
    s.sd_pin = g_st.exp[static_cast<std::size_t>(expander::Sig::SpkSd)];
    s.muted = sh.muted;
    s.playing = g_st.tone_on;
    s.configured = sh.configured;
    s.fault_pin = !g_st.exp[static_cast<std::size_t>(expander::Sig::SpkFault)];
    s.vol_pct = g_st.vol_pct;
    s.vol_db = tas5760m::db_for_pct(g_st.vol_pct);
    s.mclk_hz = g_st.spk_active ? kRateHz * g_mclk_mult : 0u;
    s.bclk_hz = g_st.spk_active ? kRateHz * 2u * g_slot_bits : 0u;
    s.sclk_hz = g_st.spk_active ? 160000000u : 0u;  // PLL_F160M, the target's default source
    s.underruns = 0;                                // nothing to starve
    s.last_error = g_start_st;
    s.last_step = g_start_step;
    s.regs_live = true;
    s.reg_digital = host::model::tas5760m_reg(0x02);
    s.reg_analog = host::model::tas5760m_reg(0x06);
    s.reg_vol = host::model::tas5760m_reg(0x04);
    s.reg_fault = host::model::tas5760m_reg(0x08);
    return Result<State>::good(s);
}

}  // namespace audio

// hal::power is NOT here.  It used to be a complete implementation on this side sitting next to
// a NotPresent stub on the other, which is two copies of the SoC endpoints and three copies of
// an open-drain inversion.  It is shared/power.cpp now -- one copy, reached through the fake ADC
// and the fake expander above, so these tests exercise the code the board runs (§11.2).

// ============================ hal::sd ====================================================
// The card is a DIRECTORY on the laptop (`clocksim --sd <dir>`, `sim sd <dir>`), mapped onto
// /sd.  No directory = no card, which is the D16 answer a board with an empty slot gives.
// The file calls themselves are shared/sd_files.cpp, the same POSIX code the target runs
// against its VFS.
namespace sd {
namespace {
std::mutex g_sd_mx;
std::string g_sd_dir;  // "" = the slot is empty
bool g_sd_mounted = false;

bool dir_exists(std::string const& d) noexcept {
    struct stat st{};
    return !d.empty() && ::stat(d.c_str(), &st) == 0 && S_ISDIR(st.st_mode);
}
}  // namespace

Status mount() noexcept {
    if (!board::present(board::Dev::Sd)) return Status::NotPresent;
    std::lock_guard lk{g_sd_mx};
    if (g_sd_mounted) return Status::Ok;
    if (!dir_exists(g_sd_dir)) return Status::NotPresent;
    g_sd_mounted = true;
    return Status::Ok;
}

Status unmount() noexcept {
    std::lock_guard lk{g_sd_mx};
    g_sd_mounted = false;
    return Status::Ok;
}

bool mounted() noexcept {
    std::lock_guard lk{g_sd_mx};
    // A card pulled out from under a mount: the directory went away.
    return g_sd_mounted && dir_exists(g_sd_dir);
}

Result<Info> info() noexcept {
    if (!mounted()) return Result<Info>::bad(Status::NotPresent);
    std::lock_guard lk{g_sd_mx};
    struct statvfs v{};
    if (::statvfs(g_sd_dir.c_str(), &v) != 0) return Result<Info>::bad(Status::Failed);
    Info in{};
    in.total_bytes = static_cast<uint64_t>(v.f_blocks) * v.f_frsize;
    in.free_bytes = static_cast<uint64_t>(v.f_bavail) * v.f_frsize;
    in.freq_khz = 20000;
    in.cluster_bytes = 32768;  // what a 32 GB FAT32 card is formatted with
    std::snprintf(in.name, sizeof in.name, "SIM");
    return Result<Info>::good(in);
}

namespace detail {
Status native_path(const char* path, char* out, std::size_t cap) noexcept {
    if (!path || std::strncmp(path, kRoot, 3) != 0 || (path[3] != '/' && path[3] != '\0'))
        return Status::BadArg;
    if (!mounted()) return Status::NotPresent;
    std::lock_guard lk{g_sd_mx};
    const int n = std::snprintf(out, cap, "%s%s", g_sd_dir.c_str(), path + 3);
    return n > 0 && static_cast<std::size_t>(n) < cap ? Status::Ok : Status::BadArg;
}
}  // namespace detail

void set_dir_host(const char* dir) noexcept {
    std::lock_guard lk{g_sd_mx};
    g_sd_dir = dir ? dir : "";
    while (g_sd_dir.size() > 1 && g_sd_dir.back() == '/') g_sd_dir.pop_back();
    g_sd_mounted = false;  // a different card: whatever was mounted is gone
}
std::string dir_host() {
    std::lock_guard lk{g_sd_mx};
    return g_sd_dir;
}
void reset_host() noexcept {
    std::lock_guard lk{g_sd_mx};
    g_sd_mounted = false;
}
}  // namespace sd

// ============================ hal::store =================================================
namespace store {

Result<int32_t> get_i32(const char* key) noexcept {
    if (!key || !*key) return Result<int32_t>::bad(Status::BadArg);
    std::lock_guard lk{g_mx};
    if (g_store_path.empty()) return Result<int32_t>::bad(Status::NotPresent);
    for (auto const& kv : g_store) {
        if (kv.key == key)
            return kv.is_str ? Result<int32_t>::bad(Status::Failed) : Result<int32_t>::good(kv.val);
    }
    return Result<int32_t>::bad(Status::NotPresent);
}

Status set_i32(const char* key, int32_t value) noexcept {
    if (!key || !*key) return Status::BadArg;
    std::lock_guard lk{g_mx};
    if (g_store_path.empty()) return Status::NotPresent;
    bool found = false;
    for (auto& kv : g_store) {
        if (kv.key == key) {
            kv.val = value;
            kv.is_str = false;
            found = true;
            break;
        }
    }
    if (!found) g_store.push_back({std::string{key}, value, {}, false});
    return store_save_locked() ? Status::Ok : Status::Failed;
}

Status get_str(const char* key, char* out, std::size_t cap) noexcept {
    if (!key || !*key || !out || cap == 0) return Status::BadArg;
    out[0] = '\0';
    std::lock_guard lk{g_mx};
    if (g_store_path.empty()) return Status::NotPresent;
    for (auto const& kv : g_store) {
        if (kv.key != key) continue;
        if (!kv.is_str || kv.str.size() >= cap) return Status::Failed;
        std::memcpy(out, kv.str.c_str(), kv.str.size() + 1);
        return Status::Ok;
    }
    return Status::NotPresent;
}

Status set_str(const char* key, const char* value) noexcept {
    if (!key || !*key || !value || std::strlen(value) >= kStrMax || std::strchr(value, '"') ||
        std::strchr(value, '\n'))
        return Status::BadArg;
    std::lock_guard lk{g_mx};
    if (g_store_path.empty()) return Status::NotPresent;
    bool found = false;
    for (auto& kv : g_store) {
        if (kv.key == key) {
            kv.str = value;
            kv.is_str = true;
            found = true;
            break;
        }
    }
    if (!found) g_store.push_back({std::string{key}, 0, std::string{value}, true});
    return store_save_locked() ? Status::Ok : Status::Failed;
}

}  // namespace store

Status init() noexcept {
    {
        std::lock_guard lk{g_mx};
        g_st.real_base_us = real_us();
    }
    // core/ owns no clock of its own (§2).  Handing it SIM time here is what makes an AO's
    // timers obey `sim warp` -- a 30-minute sunrise pre-roll watched in 30 seconds.
    port::set_clock(&clock_::micros);
    CLK_LOGI(sys, "hal: fake peripherals up (board=%s)", board::board_name());
    return Status::Ok;
}

// ============================ hal::host -- the sim control surface ========================
namespace host {

void set_warp(double f) noexcept {
    std::lock_guard lk{g_mx};
    rebase_locked();
    g_st.warp = std::clamp(f, 0.01, 10000.0);
}
double warp() noexcept {
    std::lock_guard lk{g_mx};
    return g_st.warp;
}

void advance(uint64_t us) noexcept {
    std::lock_guard lk{g_mx};
    rebase_locked();
    g_st.sim_base_us += us;
}

void set_opto(float n) noexcept {
    std::lock_guard lk{g_mx};
    g_st.opto = std::clamp(n, 0.0f, 1.0f);
    g_st.opto_auto = false;  // an explicit value wins until `sim opto auto`
}
float opto() noexcept {
    std::lock_guard lk{g_mx};
    return opto_norm_locked();
}
void set_opto_auto(bool on) noexcept {
    std::lock_guard lk{g_mx};
    g_st.opto_auto = on;
}
bool opto_auto() noexcept {
    std::lock_guard lk{g_mx};
    return g_st.opto_auto;
}

void set_vbat_mv(uint16_t mv) noexcept {
    std::lock_guard lk{g_mx};
    g_st.vbat_mv = mv;
}
void set_noise_mv(uint16_t p) noexcept {
    std::lock_guard lk{g_mx};
    g_st.noise_mv = p;
}
void set_seed(uint32_t s) noexcept {
    std::lock_guard lk{g_mx};
    g_st.rng = s ? s : 1;
}

void turn(int32_t detents) noexcept {
    std::lock_guard lk{g_mx};
    knob_settle_locked();
    g_st.count += detents * 4;
}

void turn_counts(int32_t counts) noexcept {
    std::lock_guard lk{g_mx};
    knob_settle_locked();
    g_st.count += counts;
}

// The same counts, delivered at a RATE.  A finger cannot put forty counts into one 20 ms
// poll, and since the ui paces a setting to what the hands can draw (§6.6d) the difference is
// no longer cosmetic: a lump is a spin the movement is right to refuse most of, and a ramp is
// a spin it can follow.  Anything already in flight settles first, so two overlapping turns
// add up the way two pushes of the same knob would.
void turn_counts_over(int32_t counts, uint32_t ms) noexcept {
    std::lock_guard lk{g_mx};
    knob_settle_locked();
    if (ms == 0) {
        g_st.count += counts;
        return;
    }
    g_st.turn_from = g_st.count;
    g_st.turn_to = g_st.count + counts;
    g_st.turn_t0 = sim_us_locked();
    g_st.turn_us = static_cast<uint64_t>(ms) * 1000u;
}

void press(uint32_t hold_ms) noexcept {
    std::lock_guard lk{g_mx};
    const uint64_t now = sim_us_locked();
    if (hold_ms == 0) {
        // A release: if nobody has read the closure yet, owe them one before it opens.
        if (now < g_st.sw_until_us && !g_st.sw_seen) g_st.sw_held_over = true;
    } else {
        g_st.sw_seen = false;
        g_st.sw_held_over = false;
    }
    g_st.sw_until_us = now + static_cast<uint64_t>(hold_ms) * 1000u;
}

void set_hand_angle(motor::Hand h, float deg) noexcept {
    std::lock_guard lk{g_mx};
    const int i = hand_idx(h);
    g_st.ax[i].offset_deg = wrap360(deg - axis_pos_locked(i) * 360.0 / motor::kUstepsPerRev);
}
void set_motor_jam(bool on) noexcept {
    std::lock_guard lk{g_mx};
    g_st.motor_jam = on;
    if (on) {
        axis_park_locked(0);
        axis_park_locked(1);
    }
}
void set_hand_offset(motor::Hand h, float deg) noexcept {
    std::lock_guard lk{g_mx};
    g_st.ax[hand_idx(h)].offset_deg = wrap360(deg);
}
float hand_offset(motor::Hand h) noexcept {
    std::lock_guard lk{g_mx};
    return g_st.ax[hand_idx(h)].offset_deg;
}
float hand_angle(motor::Hand h) noexcept {
    std::lock_guard lk{g_mx};
    return hand_deg_locked(hand_idx(h));
}

void set_store_path(const char* path) noexcept {
    std::lock_guard lk{g_mx};
    g_store_path = path ? path : "";
    store_load_locked();
}

const char* store_path() noexcept {
    std::lock_guard lk{g_mx};
    return g_store_path.c_str();
}

void set_orientation(float yaw, float pitch, float roll) noexcept {
    std::lock_guard lk{g_mx};
    g_st.yaw = wrap360(yaw);
    g_st.pitch = pitch;
    g_st.roll = roll;
}
void tap() noexcept {
    std::lock_guard lk{g_mx};
    ++g_st.taps;
}

// ---- the room, as the two modelled sensors would see it ---------------------------------
// These write the SCENE, not the chip: the models turn lux into counts through whatever gain
// the driver has programmed, and temperature into a raw ADC word through the datasheet's
// compensation run backwards.  So `sim lux 12000` genuinely exercises the auto-range, and
// `sim env 21.5 ...` genuinely exercises the compensation arithmetic.
void set_lux(float lux) noexcept {
    std::lock_guard lk{g_mx};
    model::set_lux(lux);
}
float lux() noexcept {
    std::lock_guard lk{g_mx};
    return model::lux();
}
void set_env(float temp_c, float rh_pct, float press_hpa, uint32_t gas_ohms) noexcept {
    std::lock_guard lk{g_mx};
    model::set_env(temp_c, rh_pct, press_hpa, gas_ohms);
}

void set_expander_in(expander::Sig s, bool level) noexcept {
    std::lock_guard lk{g_mx};
    if (static_cast<std::size_t>(s) < expander::kSigCount) {
        g_st.exp[static_cast<std::size_t>(s)] = level;
    }
}

// `sim speaker` predates hal::audio being real.  It routes through the HAL now rather than
// poking the flag, so the fake cannot end up in a state the firmware could not have reached
// -- the amp unmuted with no register set, which is what "just set spk_active" produced.
void set_speaker(bool on) noexcept { (void)audio::enable(on); }

void set_sd_dir(const char* dir) noexcept { sd::set_dir_host(dir); }
std::string sd_dir() { return sd::dir_host(); }

void set_plugged(bool p) noexcept {
    std::lock_guard lk{g_mx};
    g_st.plugged = p;
    // Unplugging drops the 12 V boost -- it is gated on PD_PG in hardware, and a fake that
    // let BOOST12_EN stay asserted across an unplug would be modelling a board that does not
    // exist (§6.8 interlock 1).
    if (!p) g_st.exp[static_cast<std::size_t>(expander::Sig::Boost12En)] = false;
}
bool plugged() noexcept {
    std::lock_guard lk{g_mx};
    return g_st.plugged;
}

void set_cell_in(bool in) noexcept {
    std::lock_guard lk{g_mx};
    g_st.cell_in = in;
}
bool cell_in() noexcept {
    std::lock_guard lk{g_mx};
    return g_st.cell_in;
}
uint32_t vbat_div_reads() noexcept {
    std::lock_guard lk{g_mx};
    return g_st.vbat_div_reads;
}

void render_pixels(char* out, std::size_t cap) noexcept {
    std::lock_guard lk{g_mx};
    std::size_t n = 0;
    for (std::size_t i = 0; i < pixels::kCount && n + 1 < cap; ++i) {
        const auto& p = g_st.px[i];
        char c = '.';
        const uint8_t mx = std::max({p.r, p.g, p.b, p.w});
        if (mx == 0)
            c = '.';
        else if (p.r == mx && p.g == mx && p.b == mx)
            c = 'W';
        else if (p.w == mx)
            c = 'W';
        else if (p.r == mx && p.g == mx)
            c = 'Y';
        else if (p.r == mx && p.b == mx)
            c = 'M';
        else if (p.g == mx && p.b == mx)
            c = 'C';
        else if (p.r == mx)
            c = 'R';
        else if (p.g == mx)
            c = 'G';
        else if (p.b == mx)
            c = 'B';
        else
            c = 'o';
        out[n++] = c;
    }
    out[n] = '\0';
}

bool refreshed() noexcept {
    std::lock_guard lk{g_mx};
    return g_st.refreshed;
}

Snapshot snapshot() noexcept {
    std::lock_guard lk{g_mx};
    Snapshot s{};
    s.sim_us = sim_us_locked();
    s.warp = g_st.warp;
    for (int i = 0; i < 2; ++i) {
        s.hand_deg[i] = hand_deg_locked(i);
        s.hand_pos[i] = static_cast<int32_t>(std::llround(axis_pos_locked(i)));
        s.hand_moving[i] = axis_moving_locked(i);
        s.hand_vel[i] = s.hand_moving[i] ? g_st.ax[i].vel : 0;
    }
    s.motor_on = g_st.motor_on;
    for (std::size_t i = 0; i < pixels::kCount; ++i) s.px[i] = g_st.px[i];
    s.refreshed = g_st.refreshed;
    s.warm_pct = g_st.warm_pct;
    s.cool_pct = g_st.cool_pct;
    s.spk_active = g_st.spk_active;
    s.vol_pct = g_st.vol_pct;
    // The CELL, not the tap.  This is the simulator's God view -- the same licence `hand_deg`
    // takes to report where a hand physically is -- so it stays truthful where power::read()
    // has to answer R-BOARD-3 honestly and say "bat node, SoC unknown".
    s.vbat_mv = g_st.vbat_mv;
    const int32_t pct =
        (static_cast<int32_t>(g_st.vbat_mv) - kVbatEmptyMv) * 100 / (kVbatFullMv - kVbatEmptyMv);
    s.soc_pct = static_cast<uint8_t>(std::clamp(pct, 0, 100));
    s.plugged = g_st.plugged;
    s.cell_in = g_st.cell_in;
    s.charging = charging_locked();
    // Raw, NOT knob::read() -- that call consumes `delta`, and a viewer that eats the ui
    // AO's deltas would be changing the thing it is watching.
    s.knob_count = knob_count_locked();
    s.knob_sw = sim_us_locked() < g_st.sw_until_us;
    s.opto = opto_norm_locked();
    s.opto_auto = g_st.opto_auto;
    s.yaw_deg = g_st.yaw;
    s.taps = g_st.taps;
    // Logical sense: the pin idles high (pulled up, toggle open) and asserts LOW.
    s.radio_off = !g_st.exp[static_cast<std::size_t>(expander::Sig::RadioOff)];
    return s;
}

// Deliberately outside g_mx: the hook does not return, so taking the lock would hand the
// next image a process whose fakes are locked by a thread that no longer exists.
RebootFn g_reboot = nullptr;

void set_reboot_hook(RebootFn f) noexcept { g_reboot = f; }

void reset() noexcept {
    std::lock_guard lk{g_mx};
    // Sim time survives.  "Fake hardware back to power-on" is not "rewind the universe":
    // time going backwards would strand every deadline an active object has already
    // computed, which is the same invariant set_warp() is careful about.
    const uint64_t keep_us = sim_us_locked();
    g_st = State{};
    g_st.sim_base_us = keep_us;
    g_st.real_base_us = real_us();
    i2c::models_reset_locked();
    // The models are the CHIPS; this is the DRIVER's shadow of one, and the two have to go
    // back to power-on together or the next test inherits a "configured" amp whose register
    // file was just wiped.
    tas5760m::forget();
    board::reset_presence();
    // The card stays in the slot (it is not "hardware state", it is what you plugged in),
    // but power-on means nothing is mounted.
    sd::reset_host();
}

}  // namespace host

// The host half of `sys reboot`.  There is no reset controller to poke, so the app that owns
// the process supplies one -- clocksim re-execs itself.  A binary that installed no hook
// (the test runner) says so rather than pretending it restarted.
Status reboot() noexcept {
    if (!host::g_reboot) return Status::NotPresent;
    host::g_reboot();
    return Status::Failed;  // only reached if the hook could not restart us
}

}  // namespace clk::hal
