tibm/clock/firmware/components/clk_hal/esp/src/hal_esp.cpp

// ESP32-S3 HAL.                                            [FIRMWARE.md §2, §12.0]
//
// STATUS, 2026-09-13: `clock_`, `adc`, `knob`, `i2c`, `pixels`, `motor`, `expander` and the
// three sensor-board drivers are real.  `hal::power` moved to shared/power.cpp -- it is
// arithmetic over the ADC and the expander and had nothing platform-specific left in it.
//
// `hal::audio` moved to esp/src/audio_esp.cpp on 2026-09-13 -- it is the only peripheral that
// owns a task, and the amp's own register set is shared/tas5760m.cpp.
//
// `wake` became real on 2026-10-01 (LEDC + the 12 V boost), which leaves no stubs here.
//
// A stub is not a placeholder apology.  On BOARD=devkit it is the *correct* answer until you
// wire something up (board_cfg starts the devkit with an empty presence mask), and D16 says
// absence is a first-class result, never a faked success and never an error log.  Each
// peripheral is independently testable the moment its part is on the breadboard, which is
// exactly why the presence mask is per-device rather than per-board.
#include <cinttypes>
#include <cstdio>
#include <cstdlib>
#include <cstring>
#include <mutex>
#include <utility>

#include "driver/gpio.h"
#include "driver/i2c_master.h"
#include "driver/ledc.h"
#include "driver/pulse_cnt.h"
#include "esp_adc/adc_cali.h"
#include "esp_adc/adc_cali_scheme.h"
#include "esp_adc/adc_oneshot.h"
#include "esp_attr.h"
#include "esp_core_dump.h"
#include "esp_err.h"
#include "esp_heap_caps.h"
#include "esp_log.h"
#include "esp_system.h"
#include "esp_timer.h"
#include "freertos/FreeRTOS.h"
#include "freertos/task.h"
#include "led_strip.h"
#include "nvs.h"
#include "nvs_flash.h"
#include "soc/rtc.h"

#include "clk/board.hpp"
#include "clk/hal/bme688.hpp"
#include "clk/hal/bno085.hpp"
#include "clk/hal/hal.hpp"
#include "clk/hal/mcp23017.hpp"
#include "clk/hal/tsl2591.hpp"
#include "clk/log.hpp"
#include "clk/port.hpp"

namespace clk::hal {

namespace clock_ {

uint64_t micros() noexcept { return static_cast<uint64_t>(esp_timer_get_time()); }
uint32_t millis() noexcept { return static_cast<uint32_t>(esp_timer_get_time() / 1000); }
void sleep_ms(uint32_t ms) noexcept { vTaskDelay(pdMS_TO_TICKS(ms)); }

// The one peripheral answer on this side that is real today, and it is real because it costs
// a register read: `esp_clk_init()` has already chosen the source by the time app_main runs,
// and it announces a fallback exactly once, in a boot log nobody is reading a week later.
SlowSrc slow_src() noexcept {
    switch (::rtc_clk_slow_src_get()) {
        case SOC_RTC_SLOW_CLK_SRC_XTAL32K:
            return SlowSrc::Xtal32k;
        case SOC_RTC_SLOW_CLK_SRC_RC_SLOW:
            return SlowSrc::RcSlow;
        case SOC_RTC_SLOW_CLK_SRC_RC_FAST_D256:
            return SlowSrc::RcFastD256;
        default:
            return SlowSrc::Unknown;
    }
}

}  // namespace clock_

// ============================ shared GPIO plumbing ========================================
namespace {

// Three pins on this board want an edge interrupt -- `SENSOR_INT` (IO42), `ENC_SW` (IO17) and
// eventually `EXPANDER_INT` (IO44) -- and IDF's per-pin ISR dispatch is installed once for the
// whole port.  Whoever gets there first installs it; ESP_ERR_INVALID_STATE means somebody
// already did, which is success and not a failure.
bool ensure_gpio_isr_service() noexcept {
    static bool ok = false;
    if (ok) return true;
    const esp_err_t e = ::gpio_install_isr_service(ESP_INTR_FLAG_LEVEL1);
    ok = (e == ESP_OK || e == ESP_ERR_INVALID_STATE);
    if (!ok) CLK_LOGE(sys, "gpio isr service: %s", ::esp_err_to_name(e));
    return ok;
}

}  // namespace

// ============================ hal::adc ===================================================
// ADC1 one-shot with curve-fitting calibration.  ADC1 and not ADC2 because ADC2 is shared
// with the Wi-Fi radio and reads fail while the radio is up -- which would present as a
// homing sensor that works perfectly until the clock joins a network.
namespace adc {
namespace {

// IO1 = ADC1_CH0 (VBAT_SENSE), IO2 = ADC1_CH1 (HOME_OPTO).  esp32.md, and kPins agrees.
constexpr adc_channel_t kChan[] = {ADC_CHANNEL_0, ADC_CHANNEL_1};
// Four conversions a read.  A single sample off a phototransistor jitters by tens of mV,
// which turns a threshold into a coin-flip; four is enough to steady the bench number and
// still costs ~100 us, well inside homing's 1 kHz poll (Section 14).
constexpr int kAvg = 4;
// The divider node is 100k||100k with C110's 100 nF across it: tau = 5 ms, so five time
// constants is 25 ms.  It only has to be paid when something asks for the cell voltage.
constexpr uint32_t kVbatSettleMs = 30;

adc_oneshot_unit_handle_t g_unit = nullptr;
adc_cali_handle_t g_cali = nullptr;
bool g_failed = false;

bool ready() noexcept {
    if (g_unit || g_failed) return g_unit != nullptr;
    adc_oneshot_unit_init_cfg_t init{};
    init.unit_id = ADC_UNIT_1;
    if (const esp_err_t e = ::adc_oneshot_new_unit(&init, &g_unit); e != ESP_OK) {
        g_unit = nullptr;
        g_failed = true;
        CLK_LOGE(drv_opto, "adc unit: %s", ::esp_err_to_name(e));
        return false;
    }
    adc_oneshot_chan_cfg_t ch{};
    // 12 dB gets the full 0-3.1 V span.  Both nodes swing most of the rail -- the opto's
    // 10k pull-up against a saturating phototransistor, and Vbat halved to ~2.1 V -- so a
    // narrower attenuation would clip the useful end of each.
    ch.atten = ADC_ATTEN_DB_12;
    ch.bitwidth = ADC_BITWIDTH_DEFAULT;
    for (const auto c : kChan) (void)::adc_oneshot_config_channel(g_unit, c, &ch);

    adc_cali_curve_fitting_config_t cal{};
    cal.unit_id = ADC_UNIT_1;
    cal.atten = ADC_ATTEN_DB_12;
    cal.bitwidth = ADC_BITWIDTH_DEFAULT;
    if (::adc_cali_create_scheme_curve_fitting(&cal, &g_cali) != ESP_OK) {
        g_cali = nullptr;  // uncalibrated: raw counts scaled, and the log says so once
        CLK_LOGW(drv_opto, "no eFuse ADC calibration; millivolts are approximate");
    }
    return true;
}

Result<uint16_t> sample(adc_channel_t c) noexcept {
    int32_t acc = 0;
    for (int i = 0; i < kAvg; ++i) {
        int raw = 0;
        if (::adc_oneshot_read(g_unit, c, &raw) != ESP_OK) {
            return Result<uint16_t>::bad(Status::Failed);
        }
        int mv = raw;
        if (g_cali) {
            if (::adc_cali_raw_to_voltage(g_cali, raw, &mv) != ESP_OK) mv = raw;
        } else {
            mv = raw * 3100 / 4095;  // nominal full scale at 12 dB; honest enough to log
        }
        acc += mv;
    }
    return Result<uint16_t>::good(static_cast<uint16_t>(acc / kAvg));
}

}  // namespace

Result<uint16_t> read_mv(Ch ch) noexcept {
    const bool vbat = ch == Ch::Vbat;
    if (!board::present(vbat ? board::Dev::Vbat : board::Dev::Opto)) {
        return Result<uint16_t>::bad(Status::NotPresent);
    }
    if (!ready()) return Result<uint16_t>::bad(Status::NotPresent);
    if (!vbat) return sample(kChan[1]);

    // Vbat sits behind Q3.  With VBAT_DIV_EN low the divider's bottom leg is OPEN, and R22
    // then pulls the ADC node up to the cell (D14 clamping it to ~3.5 V) -- a reading that
    // looks entirely plausible and means nothing.  So switch the leg in, let C110 settle,
    // read, and put it back the way it was: the default is disconnected because the divider
    // is a permanent 20 uA drain on a backup cell otherwise.
    const auto was = expander::get(expander::Sig::VbatDivEn);
    if (!was.ok()) return Result<uint16_t>::bad(was.st);
    if (const Status st = expander::set(expander::Sig::VbatDivEn, true); st != Status::Ok) {
        return Result<uint16_t>::bad(st);
    }
    clock_::sleep_ms(kVbatSettleMs);
    const auto mv = sample(kChan[0]);
    (void)expander::set(expander::Sig::VbatDivEn, was.v);
    if (!mv.ok()) return mv;
    // R22/R23 are 100k/100k, so the pin sees half the cell.  Undoing it here keeps every
    // caller in volts-at-the-cell and stops the divider ratio leaking upward.
    return Result<uint16_t>::good(static_cast<uint16_t>(mv.v * 2));
}

Result<float> read_opto_norm() noexcept {
    const auto mv = read_mv(Ch::Opto);
    if (!mv.ok()) return Result<float>::bad(mv.st);
    return Result<float>::good(opto_norm_from_mv(mv.v));
}

}  // namespace adc

// ============================ hal::knob ==================================================
// PCNT unit 0 in x4 quadrature, plus `ENC_SW` as a debounced GPIO interrupt.  Two mechanisms
// for two very different signals, and the split is the hardware's: A/B are a continuous
// position that hardware can count without us, while the push is a single event that must not
// be missed however briefly it happens (README §12 -- press is the entire mode UI).
namespace knob {
namespace {

// The EM14 is an OPTICAL encoder: 64 CPR, x4 on the quadrature decoder, 256 counts/rev, and
// no contact to bounce (§6.6d).  It also has no detent, so four counts is the notch a detented
// knob would have had -- that unit lives in `ui`, not here; the HAL counts edges.
constexpr int kHigh = 0x7FFF;  // the S3's counter is 16-bit; accum_count carries the rest
constexpr int kLow = -0x7FFF;

// 1 us rejects nothing a finger can produce -- 120 rpm at 64 CPR x4 is 512 edges a second,
// two milliseconds apart -- while killing the ringing a 5 V edge induces on its neighbour.
//
// ⚠ Bench risk worth knowing before you blame the firmware: A and B arrive through 100k/200k
// dividers (README §12), so the source impedance at the pin is ~67 k and stray capacitance
// turns each edge into a microsecond-scale ramp.  A slow ramp through a CMOS threshold is
// where a quadrature decoder invents counts.  The symptom is specific: counts moving while
// the knob is STILL, or a single detent reporting more than four.  If that happens the fix is
// the divider (10k/20k draws 0.24 mA at 5 V and is 10x stiffer), not this number -- raising
// the filter far enough to hide it would start swallowing real edges at speed.
constexpr uint32_t kGlitchNs = 1000;

// ENC_SW is a dry contact to GND with a 10 k pull-up and 100 nF on the board, so the pin is
// already RC-filtered to about a millisecond; 5 ms on top is §6.6's figure and covers the
// tail of it.  Applied as a LOCKOUT after the first falling edge rather than as a settling
// wait, because the first edge is the real one and everything within 5 ms of it is the same
// press arriving twice.
constexpr int64_t kDebounceUs = 5000;

pcnt_unit_handle_t g_unit = nullptr;
bool g_failed = false;
int32_t g_last_read = 0;
// Has ENC_SW ever been observed OPEN?  Until it has, a low reading is not a press.
//
// A person cannot be holding the knob before the firmware starts polling it, so a switch that
// reads closed from the very first read is a wiring fault, not input -- and believing it costs
// the whole UI: `ui` starts its hold timer on the first `sw`, and ten seconds later the clock
// is in BLE pairing mode with nobody having touched it.  That is what the bench saw on
// 2026-09-10.  Refusing to report a press until the pin has been seen idle turns a dead
// harness into one warning and a knob that still rotates, instead of a product stuck in a mode
// it cannot be talked out of.
bool g_sw_seen_open = false;
bool g_sw_warned = false;

// Written by the ISR, read by a task.  `g_latched` is the whole reason the press is an
// interrupt and not a poll: a closure shorter than the caller's poll period would otherwise
// not exist, and `ui` ticks at 20 ms while a quick click is easily under that.
volatile bool g_latched = false;
volatile int64_t g_last_edge_us = 0;

void IRAM_ATTR sw_isr(void*) noexcept {
    const int64_t now = ::esp_timer_get_time();
    if (now - g_last_edge_us < kDebounceUs) return;  // still inside the same press
    g_last_edge_us = now;
    if (::gpio_get_level(static_cast<gpio_num_t>(board::kPins.enc_sw)) == 0) g_latched = true;
}

bool init_sw() noexcept {
    gpio_config_t cfg{};
    cfg.pin_bit_mask = 1ULL << board::kPins.enc_sw;
    cfg.mode = GPIO_MODE_INPUT;
    // R113 is the 10 k pull-up on the board.  The internal one is in parallel with it and
    // harmless, and it is what defines the pin while J10 is unplugged -- which is most of
    // bring-up, and a floating input on an edge interrupt is an interrupt storm.
    cfg.pull_up_en = GPIO_PULLUP_ENABLE;
    cfg.intr_type = GPIO_INTR_ANYEDGE;
    if (const esp_err_t e = ::gpio_config(&cfg); e != ESP_OK) {
        CLK_LOGE(drv_knob, "ENC_SW config: %s", ::esp_err_to_name(e));
        return false;
    }
    if (!ensure_gpio_isr_service()) return false;
    return ::gpio_isr_handler_add(static_cast<gpio_num_t>(board::kPins.enc_sw), &sw_isr, nullptr) ==
           ESP_OK;
}
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
