tibm/clock/firmware/components/services/src/storage_debug.cpp

// The debug journal on the card: one text file per boot.        [FIRMWARE.md §9.4a]
//
// clk::journal keeps every log line in a 16 KB RAM ring; this drains it to
// `/sd/debug/<boot>.log` every kDbgEveryMs.  The file is opened, appended and closed each
// time, so a power cut costs at most the last few seconds and never the file -- and those
// seconds are still in `.noinit` RAM after anything short of a power cut.
//
// What the ring carried over a reset belongs to the PREVIOUS boot and goes to the end of its
// file, under a marker.  That is the useful part when the clock hangs: the task watchdog
// resets it ~10 s later, and the lines that say what it was doing are in RAM, not on the card.
//
// A file only ever GROWS.  Past kDbgFileCap a boot starts its next part, `<boot>-<part>.log`,
// instead of renaming anything -- so the phone can mirror the directory by name and size
// (`sys journal fetch`), and no file is renamed under an open download.
#include <cstdio>
#include <cstdlib>
#include <cstring>
#include <iterator>

#include "clk/journal.hpp"
#include "clk/log.hpp"
#include "clk/services/storage.hpp"

namespace clk::svc {
namespace {

constexpr const char* kKeyBoot = "sys.boot";  // NVS: the boot counter, one per app_main
constexpr uint64_t kMountRetryUs = 60'000'000;
constexpr int kMaxChunks = 8;  // per flush: 8 x 8 KB, several times the whole ring

struct DbgList {
    Storage::DbgFile* f;
    std::size_t max;
    std::size_t n = 0;
    std::size_t total = 0;
    uint64_t bytes = 0;
};
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
